DavidArmstrong/SAMDTelescopeController/TC4_0/tcheader.h

/* Telescope Controller 4.00.00 - Header file
// February 2026
// See MIT LICENSE.md file and ReadMe.md file for essential information
// Highly tailored to the AdaFruit M4 Metro
// DO NOT ATTEMPT TO LOAD THIS ONTO A STANDARD UNO */

#ifndef TC4_0_H
#define TC4_0_H
const char tcversion[] = "4.00.00";
/*=============================================================================
// Arduino SAMD Board Pin Definitions: digital from 0 to 13, Analog from 14 to 19
// D0 = Serial1 Rx - not needed, but can't be used elsewhere either
// D1 = Serial1 Tx - to 4x20 LCD
// D2 = Not Used
// D3 = Not Used
// D4 = Serial2 Rx - from XBee (Yellow wire on my cable) (SAMD51)
// Pins used for optional Reference sensors */

//const int HORIZONlim = 5; // D5 - Altitude axis Horizon reference point
//const int ZENITHlim = 6; // D6 - Altitude axis Zenith point
// D7 = Serial2 Tx - to XBee (Green wire on my cable) (SAMD51) */
const int AZREFsensor = 8; /* D8 - Azimuth axis reference point */

const int SPI_SS2 = 9; // D9 - telescope tube inclinometer sensor select
const int SPI_SS1 = 10; // D10 - Rocker Base inclinometer sensor select
// IR Detector Pin - Use TV/DVD IR Remote as a handbox control
const int IR_RECVpin = 11; /* D11 - IR Remote sensor */

// D12 = Not used
const int BLUE_LED = 13; // Blue "stat" LED on pin D13

/* D14 = A0 - Not Used
// Define Encoder Pins - Must have this if nothing else
const int RAAZ_pinA = 15; // A1 - Azimuth Encoder
const int RAAZ_pinB = 16; // A2
const int DECAL_pinA = 17; // A3 - Altitude Encoder
const int DECAL_pinB = 18; // A4 */
#define RAAZ_pinA   15
#define RAAZ_pinB   16
#define DECAL_pinA  17
#define DECAL_pinB  18

// Real Hardware button for forced re-init, position Lock, etc.
const int LOCKBTN = 19; /* A5 */
/*
// D22 = I2C SDA
// D23 = I2C SCL
// Use ICSP pins here for Murata SCA3300 inclinometer(s)
// D24 = MISO
// D26 = MOSI
// D25 = SCK */
//const int RX_LED = PIN_LED_RXL; // RX LED on pin 27, use the predefined PIN_LED_RXL to make sure
//const int TX_LED = PIN_LED_TXL; // TX LED on pin 28, use the predefined PIN_LED_TXL to make sure
/* D29-31 = USB
// D32-34 = Secondary SPI
// D35 - Secondary SPI cs

/*==========================================================================
  // I2C Addresses used
  // I2C HMC6343 Magnetic Compass (IIC address 0x19) (Not used nor referenced)
  // I2C MMC5983MA Magnetic Compass (IIC address 0x30)
  // I2C HMC6352 Magnetic Compass (IIC address 0x21, 0x41, 0x53, 0x57)
  // I2C HMC6343 Magnetic Compass (IIC address 0x32, 0x33)
  // I2C GPS receiver module (IIC address 0x42)
  // IIC address of EEPROM - 24LC256 or 24C512C-L */
//const int EEPROM_ADR = 0x55;
const int EEPROM_ADR = 0x50;
// Motor Driver config pattern "1000" on board for address 0x5D
const int MotorDriver_ADR = 0x5D; //Qwiic Motor Driver
const int LCDi2c_ADR = 0x72; //Default for Sparkfun OpenLCD
// BME280 Temperature, Barometric Pressure, Relative Humidity Sensoe I2C address
const int BME280_ADR = 0x77;

/*=======================================================================================
// Libraries!  This is why I use Arduino, seriously.

// Normally, Encoder uses attachInterrupt(), which allows dynamically attaching functions to each interrupt. The dynamic function call adds slight overhead. To eliminate this extra overhead, you can use this option. It must be defined before Encoder.h is included.
#define ENCODER_OPTIMIZE_INTERRUPTS
// This optional setting causes Encoder to use more optimized code
// The downside is a conflict if any other code in your sketch or any libraries you use require attachInterrupt(). */
#include <Encoder.h> //Optical Quadrature Encoders https://github.com/PaulStoffregen/Encoder

#include "wiring_private.h" // pinPeripheral() function for Serial2 UART
#include <Arduino.h>
#include "pins_arduino.h"
#include <Wire.h>  // Include Wire if you're using I2C
#include <stdint.h>
#include <string.h>

#include "RTC_SAMD51.h" // https://github.com/Seeed-Studio/Seeed_Arduino_RTC
#include "DateTime.h"

#include <math.h> //Oh yeah.....
#include "SiderealPlanets.h" //Astronomy routines https://github.com/DavidArmstrong/SiderealPlanets
#include "SiderealObjects.h" //Astronomy Tables https://github.com/DavidArmstrong/SiderealObjects
#include <curveFitting.h> // https://github.com/Rotario/arduinoCurveFitting

#include "extEEPROM.h" // I2C EEPROM https://github.com/PaoloP74/extEEPROM
#include <SerLCD.h> //Serial LCD library: https://github.com/sparkfun/SparkFun_SerLCD_Arduino_Library
#include "ansi.h" // VT100 support https://github.com/RobTillaart/ANSI
#include <SparkFun_u-blox_GNSS_Arduino_Library.h> //Click here to get the library: https://github.com/sparkfun/SparkFun_u-blox_GNSS_Arduino_Library
#include "SparkFunBME280.h" //Temperature, Pressure, Humidity sensor https://github.com/sparkfun/SparkFun_BME280_Arduino_Library

#include <IRLibDecodeBase.h> // First include the decode base https://github.com/cyborg5/IRLib2 
#include <IRLib_P01_NEC.h>   // Now include only the protocols you wish
#include <IRLib_P02_Sony.h>  // to actually use. The lowest numbered
#include <IRLib_P07_NECx.h>  // must be first but others can be any order.
//#include <IRLib_P09_GICable.h>
//#include <IRLib_P11_RCMM.h>
#include <IRLibCombo.h>     // After all protocols, include this
// All of the above automatically creates a universal decoder
// class called "IRdecode" containing only the protocols you want.
#include <IRLibRecv.h>

#include "SCMD.h" // Serial Controlled Motor Driver https://github.com/sparkfun/Serial_Controlled_Motor_Driver
#include "SCMD_config.h" //Contains #defines for common SCMD register names and values
#include "SAMD51_InterruptTimer.h"

// Magnetic Compass Libraries
#ifdef __HMC6352__
#include <HMC6352.h> // https://github.com/funflin/HMC6352-Arduino-Library
#endif
#ifdef __HMC6343__
#include "SFE_HMC6343.h" // https://github.com/sparkfun/SparkFun_HMC6343_Arduino_Library
#endif
#include <SparkFun_MMC5983MA_Arduino_Library.h> //Click here to get the library: http://librarymanager/All#SparkFun_MMC5983MA
// https://github.com/sparkfun/SparkFun_MMC5983MA_Magnetometer_Arduino_Library

#include "WMM_Tinier.h" // WMM Magnetic variation - https://github.com/DavidArmstrong/WMM_Tinier

#include <SPI.h> //Need for Murata inclinometer sensor
#include "SCL3300.h" // https://github.com/DavidArmstrong/Arduino-SCL3300

//=========================================
// EEPROM definitions
const int MAXUCOORD = 200; // maximum number of User Defined Coordinates
const int EEcheckByte = 0x54;
struct EEstruct {
  double dummy;
  double FtiltXrockeroff;
  double FtiltYrockeroff;
  double FtiltXtubeoff;
  double FtiltYtubeoff;
  double FLATITUDE;
  double FLONGITUDE;
  float DTEMPF; // default Farenheit temperature
  float DTZONE; // Default Time zone offset from GMT
  float azKp, azKi, azKd, alKp, alKi, alKd; // motor PID scaling values
  float azN, alN; // motor PID damping intervals
  // IR decode Table - 24 chars match one of 20 long numbers
  long IRinput[32]; // Raw IR remote button numbers
  char IRchar[32]; // Corresponding ASCII char for each number
  // User defined coordinates
  long UCOORD[MAXUCOORD * 2]; // save space for user defined objects
  long RRAAZ; //Default encoder range for RA/Azimuth
  long RDECAL; //Default encoder range for Declination/Altitude
  long AZOFFSET; //Encoder count Offset of Azimuth Reference Sensor from True North
  long ALOFFSET; //Encoder count Offset of Altitude Horizon Sensor from Level with horizon
  long AzTweakOffsetCounts, AlTweakOffsetCounts; // Count offsets based on last star sync
  int ELEVATION; // default elevation
  int EEchk;
  int LCDbrightness;
  int HbxSpeed;
  boolean DSTFLAG; // Set to true if Daylight Savings time is in effect
  boolean USELIMITS; //using Limits?
  boolean ERRFLAG; // error variable flag
  boolean PFLAG;  // Precession flag
  boolean RFLAG;  // True if Refraction calculations enabled
  boolean MotorDriverflag;
  boolean LCDserialflag; // PIC-based LCD display used?
  boolean LCDavrflag; // OpenLCD I2C display used?
  //Note: if both LCDserialflag and LCDavrflag are true, then an OpenLCD device is on TC_LCD
  boolean IRSETUPflag; // Set if IR remote has been set up
  boolean TCIFLAG; // Set if Telescope Control interface is configured
  boolean INA219flag; // INA219 I2C voltage monior used?
  char SiteID[40];
  boolean SerialTermflag; // Serial Terminal output Updated regularly?
  boolean AzRangeMeasured;
  boolean enableRealHwInit;
};

union EEarray {
  EEstruct strunion;
  byte ebuf[sizeof(EEstruct)];
} eecharbuf;

// 256 kbits = 32K bytes for EEPROM
//extEEPROM tcEEPROM(kbits_256, 1, 64, EEPROM_ADR);
// 512 kbits = 64K bytes for EEPROM
extEEPROM tcEEPROM(kbits_512, 1, 64, EEPROM_ADR);

//=======================================================
// Structure to hold data
// We need to populate this when we calculate data
struct DobsonianControlData {
  public:
    long int azimuthEncoder;
    long int altitudeEncoder;
    long int maxAzimuthCount;
    long int maxAltitudeCount;
    long int azimuthOffset;
    long int altitudeOffset;
    float declination; // magnetic variation from True North
};

DobsonianControlData spData;

/*=======================================================
  // Define stuff for compatibility with translated
  // Telescope Controller code (Originally in Forth)
  // Commands available in the system */
#define SETIMECMD 0x1c
#define FNDOBJECT 0x1d
#define INITCMD 0x1e
#define FNDARB 0x1f
// Stay at current telescope position
#define STAYFUNC 0x22

// Motor Defines to make it more readable
#define ALTITUDE_MOTOR 0
#define AZIMUTH_MOTOR 1
#define CW_DIRECTION 0
#define CCW_DIRECTION 1
#define STOP_SPEED 0
#define SLOW_SPEED 5
#define FAST_SPEED 255

// User variables
long IRkey; // Record latest raw IR key code, if seen
boolean lockbtninitflag;
byte COMMAND; //What the User tells us to do
byte screenCOMMAND;
boolean screenDecRefresh;
byte LCDscreenNum;
boolean TCIFLAG; // Set to true if Telescope Control interface has been set up
boolean displayFLAG; // Set to true if display option has been selected
boolean AUTOSTARFLAG;  // Set to true if system can offer to select alignment star
boolean INITFLAG;  // Telescope mount initialized flag
boolean TIMEFLAG;  // Time initialized flag
boolean DSTFLAG;  // Set to true if Daylight Savings time is in effect
boolean DSTAUTOFLAG; // Set to true if we automatically compute if DST is in effect - US Only

byte inputstrlen;

long RAAZ;  // Current encoder counts in RA/Azimuth
long DECAL;  // Current encoder counts in Declination/Altitude
long TcRAAZ;  // Target encoder counts in RA/Azimuth
long TcDECAL;  // Target encoder counts in Declination/Altitude
long RRAAZ;  // Known rangle of encoder counts in RA/Azimuth
long RDECAL;  // Known rangle of encoder counts in Declination/Altitude
double previousTRA, previousTDEC;
double TAZIMUTH; // Target Azimuth in degrees from North - used in Displays
double TALTITUDE; // Target Altitude in degrees

long LATEMP;
double FALTEMP;  // store floating # altitude
int GRYEAR;
byte GRMONTH, GRDAY;
long TIMER; //Double seconds time count
int rtcseconds, rtcmin, rtchours;
int hmsseconds, hmsmin, hmshours;
char siteid[70];

double FLONGITUDE, FLATITUDE;  // degrees
double FAZIMUTH, FALTITUDE; // degrees
double FRA, FDEC; // Current RA in hours, Declination in degrees
double TRA;  // Target RA in hours
double TDEC;  // Target Declination in degrees

boolean ERRFLAG;  // error variable flag
double FHEIGHT;  // FP elevation in feet
double FTEMPF;  // Temperature in Farenheit for refraction
double FHUMID; // Percent relative humidity
double FPINHG;  // Barometric Pressure in Inches of Mercury
double FELAT;  // Equatorial Mount Latitude
double FMAGHDG; // Magnetic Compass heading
float magVariation; // Magnetic Declination or Variation
long magVariationInAzimuthCounts;
long AzimuthMagneticEncoderOffset;
boolean magOffsetComputed;
long AzTweakOffsetCounts, AlTweakOffsetCounts;
int LCDbrightness;

// need to make auto star select table
const int ISTARS[] = {
  98  , /* Aldebaran */         492 , /* Vega */
  113 , /* Rigel */             529 , /* Altair */
  114 , /* Capella */           547 , /* Deneb */
  140 , /* Betelgeuse */        595 , /* Markab */
  162 , /* Sirius */            43  , /* Hamal */
  190 , /* Procyon */           30  , /* Achernar */
  196 , /* Pollux */            47  , /* Mira */
  188 , /* Castor */            62  , /* Algol */
  254 , /* Regulus */           155 , /* Canopus */
  350 , /* Arcturus */          330 , /* Mizar */
  422 , /* Antares */           592   /* Fomalhaut */
};
const byte NISTARS = 22; // number of stars in table

const char hitkey[] = "Hit Key to continue";

// define IR receive pin - for IR Remote Library routines
int RECV_PIN = IR_RECVpin;
//decode_results results;
boolean irsetup, IRFLAG;
char irkeytab[20];

/*======================================================================
// Library specific variable defines
// For second UART port - SAMD51 can only have TX on PAD 0 */
#define PIN_SERIAL2_RX 4    /* PB13 */
#define PAD_SERIAL2_RX (SERCOM_RX_PAD_1)
#define PIN_SERIAL2_TX 7    /* PB12 */
#define PAD_SERIAL2_TX (UART_TX_PAD_0)
Uart Serial2( &sercom4, PIN_SERIAL2_RX, PIN_SERIAL2_TX, PAD_SERIAL2_RX, PAD_SERIAL2_TX );
Stream *SERIALOUT = &Serial2;
/* RX: SERCOM4/PAD[1] = D4 = PB13
// TX: SERCOM4/PAD[0] = D7 = PB12 */

#ifndef SWAP_AZIMUTH_ENCODER_AB
Encoder RAAZenc( RAAZ_pinA , RAAZ_pinB ); //Incremental Quadrature Encoder for RA/Aximuth
#else
Encoder RAAZenc( RAAZ_pinB , RAAZ_pinA ); //Incremental Quadrature Encoder for RA/Aximuth
#endif

// Now declare an instance of that decoder.
IRdecode irdecoder;
IRrecv irrecv(RECV_PIN);  //pin number for the receiver
RTC_SAMD51 rtczero;

BME280 bme280; //Temperature, Barometric Pressure, Humidity Sensor
SFE_UBLOX_GNSS ubloxGPS;
boolean I2CEEPROMpresent, GPSpresent, BMEpresent;
SiderealPlanets myAstro;
SiderealObjects myObjects;
boolean MotorDriverflag;
SCMD i2cMotorDriver; //Serial Controlled Motor Driver

boolean MagCompasspresent;
boolean HMC6343MagCompasspresent;
boolean MMC5983MAMagCompasspresent;
#ifdef __HMC6343__
SFE_HMC6343 dobHMC6343; // Declare the compass object
#endif
SFE_MMC5983MA MMC5983MAmag;
WMM_Tinier myDeclination;
SCL3300 rockerTilt, tubeTilt; // inclinometers
boolean rockerTiltPresent, tubeTiltPresent;
ANSI ansi(&TCterminal); // VT100 support
boolean AzimuthEncoderInitialized;
int currentAzMtrSpeed, currentAlMtrSpeed;
int currentAzMtrDir, currentAlMtrDir;
unsigned long AzPreviousMillis, AlPreviousMillis;
float azKp, azKi, azKd, alKp, alKi, alKd; // motor PID scaling values
float azN, alN; // motor PID damping intervals
float azTau, alTau;
float azError[3] = { 0., 0., 0. };
float alError[3] = { 0., 0., 0. };
float azD0, azD1, azFd0, azFd1;
float alD0, alD1, alFd0, alFd1;
boolean PIDFLAG;

#ifndef __FUNCTIONDECLARATIONS__
//===============================================
// need to declare all functions - whatever
// TCVCIOFP
char KEY();
void EMIT(char n);
long GETnum(char* buf);
void LCDline1();
void LCDline2();
void LCDline3();
void LCDline4();
void LCDclear();
void LCDbrighter();
void LCDdimmer();
void LCDprint(int tmp);
void LCDprint(long tmp);
void LCDprint(double tmp, int frac);
void LCDprint(char tmp);
void LCDprint(char* tmp);
void LCDprint(const char* tmp);
void SETINITFLAG();
void RESETINITFLAG();
boolean NOTINITquestion();
void SETIMEFLAG();
void RESETIMEFLAG();
boolean NOTIMESETquestion();
boolean INITCOMMANDquestion();
boolean TIMECOMMANDquestion();
void SETIRFLAG();
void RESETIRFLAG();
boolean IRquestion();
void SETTCIFLAG();
void RESETTCIFLAG();
boolean TCIquestion();
void SETdisplayFLAG();
void RESETdisplayFLAG();
boolean Displayquestion();
void SETPIDFLAG();
void RESETPIDFLAG();
boolean PIDquestion();
void SETERRFLAG();
void RESETERRFLAG();
int ACCEPT(char *buf, int limit);
boolean RDLBTN();
void TERMclear();
void TERMlineup();
void TERMcursor();
void TERMxy(int x, int y);
void TERMtextcolor( char buf );
void WAITASEC(int n);
void newdelay( long interval );
boolean CHKNUM();
#ifdef __HMC6352__
boolean getMagCompassPresent(void);
#endif
#ifdef __HMC6343__
boolean get6343MagCompassPresent(void);
#endif
float magneticDeclination(float Latitude, float Longitude, uint8_t year, uint8_t month, uint8_t day);
float getMagCompassHeading(void);
double getMMC5983MagCompassHeading(void);
boolean getRockerTiltPresent(void);
boolean getTubeTiltPresent(void);
double getAltitude(void);
double getAzimuth(void);
boolean getAzRefSensor();
boolean startMotorToTarget(int motor, int direction, unsigned long currentPosition, unsigned long targetPosition);
boolean driveMotor(int motor, int direction, int speed);
boolean driveMotorStop(int motor);

// TCDERVIO
void printDegMinSecs(double n);
void printDegMinSecsLCD(double n);
void printTime(double n);
void printTimeLCD(double n);
void print2digits(int number);
void print2digitsUSB(int number);
void print2digitsLCD(int number);
boolean TRPLCMP( int n1, int n2, int n3, int n4 );
boolean GETYORN();
long GETDDECNUM();
int GETINUM();
int GETINUM(int n);
long CONVHMS(char *buf);
long INPUTHMS();
double GETFDECNUM();
double GETFDECNUM(float n);

// TCUSERIO
void printstatusscreen();
void showDate();
void showDateLCD();
void printObject();
void printObjectLCD();
void updatestatusscreen();
void updatestatusLCD();
void TERMALLOPTIONS();
void PRPLANET( int n );
void PRPLANETlcd( int n );

// TCINIT
void SERCOM4_0_Handler();
void SERCOM4_1_Handler();
void SERCOM4_2_Handler();
void SERCOM4_3_Handler();
void eepromDefaults();
void rockertiltlevelcheck();
void gotoAzRef();
void measureAZrange();
void getMagneticNorth();
double getTubeTiltX();
void inithardware();
void STRTturboCLK();
void INITZONE();
void RESETIME();
void INIT();
long initIRkey(long previous);
void RESETIR();
void OptionStateMsg(boolean flag);
void LCDOptionStateMsg(boolean flag);
void RESETTCI();
void RESETdisplay();
void topEEPROMwrite();
void gotoTarget();
void doCommand();
void tcintro();
void TC_main();
#endif
#endif
