DavidArmstrong/SAMDTelescopeController/TC4_0/tcinit.ino

/* Telescope Controller 4.00.00 - Initialization and High level functionality
// February 2026
// See MIT LICENSE.md file and ReadMe.md file for essential information
// Highly tailored to the AdaFruit M4 Metro
// DO NOT ATTEMPT TO LOAD THIS ONTO A STANDARD UNO */

#include "tcheader.h"

/* We have to define this function to use the SAMD51 alternate Serial2 pins
// And for SAMD51 on the Metro M4 - can't use sercom5, 3, or 2
// sercom3 - Serial1 on D0/D1
// sercom5 - I2C pins for SCL/SDA
// sercom2 - SPI */
#ifdef _VARIANT_SAMD51_MICROMOD_
#else
void SERCOM4_0_Handler() { Serial2.IrqHandler(); }
void SERCOM4_1_Handler() { Serial2.IrqHandler(); }
void SERCOM4_2_Handler() { Serial2.IrqHandler(); }
void SERCOM4_3_Handler() { Serial2.IrqHandler(); }
#endif

void eepromDefaults() {
  // Default values that we start with on a new EEPROM
  IRkey = 0L;
  // Brute force default initialization of EEPROM variables
  // We will replace the defaults if valid data is in an EEPROM
  eecharbuf.strunion.EEchk = 0; // Check for existence of EEPROM
  //eecharbuf.strunion.DSTFLAG = false; // Daylight Savings used
  eecharbuf.strunion.USELIMITS = false; // Using Limit/reference sensors?
  eecharbuf.strunion.ERRFLAG = false; // Errors flag
  eecharbuf.strunion.PFLAG = false; // Precession flag
  eecharbuf.strunion.RFLAG = false; // Refraction flag
  eecharbuf.strunion.MotorDriverflag = false; // Motor driver flag
  eecharbuf.strunion.SerialTermflag = true; // Serial port Terminal display
  eecharbuf.strunion.LCDserialflag = false; // PIC-based or AVR-based LCD on Serial used?
  eecharbuf.strunion.LCDavrflag = false; // AVR LCD on IIC?
  eecharbuf.strunion.LCDbrightness = 255; // Full brightness for LCD backlight
  eecharbuf.strunion.IRSETUPflag = irsetup = false; // IR remote in use
  eecharbuf.strunion.TCIFLAG = TCIFLAG = false; // Telescope Control Interface set up
  eecharbuf.strunion.ELEVATION = 5500; // Elevation in feet
  eecharbuf.strunion.RRAAZ = 10000L; // Azimuth encoder range
  eecharbuf.strunion.RDECAL = pow(2, 14); // Altitude encoder range
  eecharbuf.strunion.AZOFFSET = 0L; // Encoder count Offset of Azimuth Reference from True North
  eecharbuf.strunion.ALOFFSET = 0L; // Encoder count Offset of Altitude Horizon Reference from level
  eecharbuf.strunion.AzTweakOffsetCounts = 0L; // Count offsets based on last star sync
  eecharbuf.strunion.AlTweakOffsetCounts = 0L;
  AzTweakOffsetCounts = AlTweakOffsetCounts = 0L;
  eecharbuf.strunion.DTEMPF = 68.0; // Default temp in Farenheit
  //eecharbuf.strunion.DTZONE = -8.0; // Default Time Zone (PST)
  eecharbuf.strunion.FLATITUDE = 1.; // Latitude in radians
  eecharbuf.strunion.FLONGITUDE = -1.; // Longitude in radians, West is negative
  strncpy ( eecharbuf.strunion.SiteID, "Demo mode", sizeof("Demo mode") );
  eecharbuf.strunion.AzRangeMeasured = false;
  eecharbuf.strunion.FtiltXrockeroff = 0.; // Offset of X Tilt on Rocker from level
  eecharbuf.strunion.FtiltYrockeroff = 0.; // Offset of Y Tilt on Rocker from level
  eecharbuf.strunion.FtiltXtubeoff = 0.; // Offset of X Tilt on Telescope Tube from level
  eecharbuf.strunion.FtiltYtubeoff = 0.; // Offset of Y Tilt on Telescope Tube from level
  // Set up default values for Demo mode
  //DSTFLAG = eecharbuf.strunion.DSTFLAG;
  // Assume Demo mode on initial boot
  eecharbuf.strunion.enableRealHwInit = false;
  MotorDriverflag = eecharbuf.strunion.MotorDriverflag;
  // PID scaling values - We guess at these, or determine them empirically
  eecharbuf.strunion.azKp = 1.0; // Azimuth motor Proportional gain
  eecharbuf.strunion.azKi = 1.0; // Azimuth motor Integral gain
  eecharbuf.strunion.azKd = 1.0; // Azimuth motor Derivative gain
  eecharbuf.strunion.azN  = 5; // Azimuth derivative low pass filter time constant, 3 <= N <= 10
  eecharbuf.strunion.alKp = 1.0; // Altitude motor Proportional gain
  eecharbuf.strunion.alKi = 1.0; // Altitude motor Integral gain
  eecharbuf.strunion.alKd = 1.0; // Altitude motor Derivative gain
  eecharbuf.strunion.alN  = 5; // Altitude derivative low pass filter time constant, 3 <= N <= 10
  // Offset of Azimuth Encoder Range from measured Magnetic North
  AzimuthMagneticEncoderOffset = 0.;
  magOffsetComputed = false;
  LCDbrightness = 0x9D; // Default LCD backlight brightness is MAX
  RAAZenc.write(0L);
  FAZIMUTH = 0.;
  //DECALenc.write(0L);
  FALTITUDE = 0.;
}

void rockertiltlevelcheck() {
  // Telescope should already be parked on boot so leveling access holes are reachable
  int i = 0;

  TCterminal.println("");
  TCterminal.println("Check Rocker Level:");
  TCterminal.println(hitkey);

  LCDline2();
  LCDprint("Check Level:");
  LCDline4();
  LCDprint(hitkey);

  while (!CHKNUM()) {
    if (rockerTilt.isConnected()) {
      //Get next block of data from sensor
      if (rockerTilt.available()) {
        if (eecharbuf.strunion.SerialTermflag) {
          // print Base tilt
          TCterminal.println("");
          TCterminal.print(rockerTilt.getTiltLevelOffsetAngleX() - eecharbuf.strunion.FtiltXrockeroff);
          TCterminal.print("  ");
          TCterminal.print(rockerTilt.getTiltLevelOffsetAngleY() - eecharbuf.strunion.FtiltYrockeroff);
          TCterminal.print("  ");
          TERMlineup();
          LCDline3();
          LCDprint(rockerTilt.getTiltLevelOffsetAngleX() - eecharbuf.strunion.FtiltXrockeroff, 2);
          LCDprint("  ");
          LCDprint(rockerTilt.getTiltLevelOffsetAngleY() - eecharbuf.strunion.FtiltYrockeroff, 2);
          LCDprint("  ");
          newdelay(500);
        }
        } else rockerTilt.reset();
      } else rockerTilt.reset();
    }
    KEY();
  TCterminal.println("");
  LCDclear();
}

void gotoAzRef() {
  //If Azimuth Reference Sensor, use that
  if (eecharbuf.strunion.USELIMITS) {
    // Start by finding the Azimuth Reference Sensor.
    if (getAzRefSensor()) {
      // We're on the sensor, so get off it.
      if (MotorDriverflag) {
        //Run the motor CCW to get off of it
        driveMotor(AZIMUTH_MOTOR, CCW_DIRECTION, FAST_SPEED);
      } else {
        TCterminal.println("Move telescope in Azimuth CCW to get off of AZ Reference Sensor.");
        TCterminal.println(hitkey);
        LCDclear();
        LCDline2();
        LCDprint("Move Azimuth CCW");
        LCDline4();
        LCDprint(hitkey);
        KEY();
      }
      // And wait....
      while (getAzRefSensor()) ;
      driveMotorStop(AZIMUTH_MOTOR); // Turn motor off
    }
    if (MotorDriverflag) {
      newdelay(500);
      // Start motor in CW direction to find Azimuth Reference Sensor
      driveMotor(AZIMUTH_MOTOR, CW_DIRECTION, FAST_SPEED);
    } else {
      TCterminal.println("Move telescope in Azimuth CW to find AZ Reference Sensor.");
      LCDclear();
      LCDline2();
      LCDprint("Move Azimuth CCW");
    }
    // Continue  until we find the AZ ref sensor
    while (!getAzRefSensor()) ;
    // We hit it, so zero the Encoder counts
  } else {
    TCterminal.println("Move telescope in Azimuth to select an AZ Reference position. (i.e. North)");
    TCterminal.println(hitkey);
    LCDclear();
    LCDline1();
    LCDprint("Move Azimuth");
    LCDline2();
    LCDprint("to Reference Pt");
    LCDline3();
    LCDprint("(i.e. North)");
    LCDline4();
    LCDprint(hitkey);
    KEY();
  }
  RAAZenc.write(0L);
  RAAZ = 0L;
}

void measureAZrange() {
  // Need to play the game to measure how many encoder counts make one revolution in Azimuth
  gotoAzRef();
  // And keep going to get off the sensor
  if (!MotorDriverflag) {
    TCterminal.println("Keep moving telescope in Azimuth CW to find AZ Reference ");
    LCDclear();
    LCDline1();
    LCDprint("Move Azimuth CW");
    LCDline2();
    
    if (eecharbuf.strunion.USELIMITS) {
      TCterminal.println("Sensor again.");
      LCDprint("to Reference Pt");
    } else {
      TCterminal.println("position again. (i.e. North)");
      LCDprint("to North");
    }
    LCDline3();
    LCDprint("again");
  }
  
  if (eecharbuf.strunion.USELIMITS) {
    while (getAzRefSensor()) ;
    // And keep running until we hit the AZ ref sensor again
    newdelay(100);
    while (!getAzRefSensor()) ;
  } else {
    TCterminal.println(hitkey);
    LCDline4();
    LCDprint(hitkey);
    KEY();
  }
  RAAZ = RRAAZ = eecharbuf.strunion.RRAAZ = RAAZenc.read();
  eecharbuf.strunion.AzRangeMeasured = true;
  AzimuthEncoderInitialized = true;
  if (!MotorDriverflag) {
    if (eecharbuf.strunion.USELIMITS) TCterminal.print("Hit AZ Reference Sensor again. ");
    TCterminal.print("AZ Range is: ");
    TCterminal.print(eecharbuf.strunion.RRAAZ);
    LCDclear();
    LCDline1();
    LCDprint("AZ Range is:");
    LCDline2();
    LCDprint(RRAAZ);
  } else {
    driveMotorStop(AZIMUTH_MOTOR); // Stop motor and From now on, ignore the Azimuth Reference Sensor
  }
  newdelay(500);
  // Next, we need the offsets for the Rocker inclinometer in X and Y from true level
  if (getRockerTiltPresent()) {
    double FtiltXrockerHi = 0.;
    double FtiltYrockerHi = 0.;
    double FtiltXrockerLo = 0.;
    double FtiltYrockerLo = 0.;
    double Xtilt, Ytilt;
    rockerTilt.setFastReadMode();
    if (!MotorDriverflag) {
      TCterminal.println("Move telescope in Azimuth back around CCW to find AZ Inclinometer Offsets.");
      LCDclear();
      LCDline1();
      LCDprint("Move Azimuth CCW");
      LCDline2();
      LCDprint("to find");
      LCDline3();
      LCDprint("SCL3300 offsets");
    } else {
      // Turn Azimuth motor on CCW towards zero
      driveMotor(AZIMUTH_MOTOR, CCW_DIRECTION, SLOW_SPEED);
    }
    while ( RAAZenc.read() > 0 ) {
      //Get next block of data from sensor
      if (rockerTilt.available()) {
        // print Base tilt
        Xtilt = rockerTilt.getTiltLevelOffsetAngleX();
        Ytilt = rockerTilt.getTiltLevelOffsetAngleY();
        if (Xtilt > FtiltXrockerHi) FtiltXrockerHi = Xtilt;
        if (Xtilt < FtiltXrockerLo) FtiltXrockerLo = Xtilt;
        if (Ytilt > FtiltYrockerHi) FtiltYrockerHi = Ytilt;
        if (Ytilt < FtiltYrockerLo) FtiltYrockerLo = Ytilt;
      } else rockerTilt.reset();
    }
    rockerTilt.stopFastReadMode();
    eecharbuf.strunion.FtiltXrockeroff = (FtiltXrockerHi + FtiltXrockerLo) / 2.;
    eecharbuf.strunion.FtiltYrockeroff = (FtiltYrockerHi + FtiltYrockerLo) / 2.;
    if (!MotorDriverflag) {
      TCterminal.println("AZ Inclinometer Offsets computed.");
    } else {
      // And turn motor Off
      driveMotorStop(AZIMUTH_MOTOR);
    }
    //`Allow User to Level the Bottom Board now....
    rockertiltlevelcheck();
  }
}

void getMagneticNorth() {
  // Use a magnetic compass to figure out the offset between the current
  // Azimuth zero reference point, and Magnetic North
  int order = 1;
  double x[3600], y[3600], n;
  double x0[3600], y0[3600], n0;
  double coeffs[order+1];
  char buf[100];
  int i, j, max, min, guessNorth;
  
  // We only do this if we are using Motors so as to avoid magnetic noise
  if (MotorDriverflag && (
#ifdef __HMC6352__
  getMagCompassPresent() ||
#endif
#ifdef __HMC6343__
  HMC6343MagCompasspresent ||
#endif
  MMC5983MAMagCompasspresent)) {
    // Prompt User to prep for Magnetic Compass
	TCterminal.println("");
    TCterminal.println("Check Magnetic Compass position:");
    TCterminal.println(hitkey);
    LCDclear();
    LCDline1();
    LCDprint("Check Mag Compass");
    LCDline4();
    LCDprint(hitkey);
	KEY();
#ifdef __HMC6352__
	if (getMagCompassPresent()) {
	  HMC6352.Wake();
      newdelay(10);
	}
#endif
	// We start with a game to get a 'full' circle in Azimuth
	driveMotor(AZIMUTH_MOTOR, CCW_DIRECTION, FAST_SPEED); // Go backwards past zero point
	while (RAAZenc.read() > 0L) ; // wait until past it
	driveMotorStop(AZIMUTH_MOTOR); // Stop the motor
	// Turn Azimuth motor on going CW around
	driveMotor(AZIMUTH_MOTOR, CW_DIRECTION, FAST_SPEED);
	while (RAAZenc.read() < 0L) ; // wait until we reach zero
    // GO! - Get data points - Assume we are starting at Azimuth = 0
	y[3599] = 0.;
    for (i = 0; i < 3600; i++) {
	  // wait until we get to the next point
	  while ((RAAZenc.read() * 3600L / RRAAZ) % 3600L != 0L) ;
	  x[1] = (double) RAAZenc.read();
#ifdef __HMC6352__
	  if (getMagCompassPresent()) y[i] = (double) HMC6352.GetHeading();
#endif
	  if (MMC5983MAMagCompasspresent) y[i] = getMMC5983MagCompassHeading();
	  while ((RAAZenc.read() * 3600L / RRAAZ) % 3600L == 0L) ; // wait until off this point
	}
	driveMotorStop(AZIMUTH_MOTOR); // Stop the motor
	// Now we most likely have a sawtooth pattern of magnetic readings
	// Need to move the data points around so it's more-or-less a line
	// Start by finding the max and min magnetic compass points in the array
	max = 0;
	min = 3600;
	for (i = 0; i < 3600; i++) {
      if (y[i] > y[max]) max = i;
	  if (y[i] < y[min]) min = i;
	}
	// We guess that average between min and max is where magnetic North is
	guessNorth = (max + min) / 2;
	// And shift the data arrays accordingly so we can do a reasonable curve fit
    for (i = 0; i < 3599; i++) {
      j = i + guessNorth;
	  if (j > 3599) {
        j -= 3600;
	  }
	  y0[i] = y[j]; // Magnetic Compass reading
	  x0[i] = x[j]; // Encoder position
	}
	TCterminal.print("Needed to shift array by about ");
	TCterminal.print(guessNorth * (RRAAZ / 3600L));
	TCterminal.println(" encoder counts");
	// And now we do the curve fit
    int ret = fitCurve(order, sizeof(y0)/sizeof(double), x0, y0, sizeof(coeffs)/sizeof(double), coeffs);
  
    if (ret == 0) { //Returned value is 0 if no error
      uint8_t c = 'a';
      TCterminal.println("Coefficients are");
      for (int i = 0; i < sizeof(coeffs)/sizeof(double); i++) {
        snprintf(buf, 100, "%c=",c++);
        TCterminal.print(buf);
        TCterminal.print(coeffs[i]);
        TCterminal.print('\t');
      }
	  // Save Magnetic offset
      // Later, it will be used with Magnetic Variation, and current Azimuth range
	  // So that location '0' is True North
	  AzimuthMagneticEncoderOffset = ((float)guessNorth * ((float)RRAAZ / 3600.)) + (-coeffs[1] / coeffs[0]);
    } else {
	  TCterminal.println("Error in computing Curve fit of data");
	  TCterminal.println("Making a guess of where Magnetic North is in Encoder counts.");
	  AzimuthMagneticEncoderOffset = (float)guessNorth * ((float)RRAAZ / 3600.);
    }
	magOffsetComputed = true;
	TCterminal.println("");
    TCterminal.println("Retract Magnetic Compass position:");
    TCterminal.println(hitkey);
    LCDclear();
    LCDline1();
    LCDprint("Retract Mag Compass");
    LCDline4();
    LCDprint(hitkey);
	KEY();
  }
}


double getTubeTiltX() {
  // Return only the Telescope Optical tube tilt in the X direction on the sensor
  // We will do this by cheating horribly and accept a value even if there is an error
  tubeTilt.available();
  return tubeTilt.getTiltLevelOffsetAngleX();
}

void inithardware() { //Set up all the hardware interfaces
  // Read Hardware button for forced re-init, position Lock, etc.
  pinMode(LOCKBTN, INPUT_PULLUP);
  lockbtninitflag = RDLBTN(); //Get button state, first thing
  // initialize digital pin LED_BUILTIN as an output.
  pinMode(LED_BUILTIN, OUTPUT);
  pinMode(AZREFsensor, INPUT_PULLUP);
  
  eepromDefaults();
  AzimuthEncoderInitialized = false;

  // verify presence of I2C EEPROM
  byte EEPROMstatus = tcEEPROM.begin(extEEPROM::twiClock100kHz);
  I2CEEPROMpresent = true;
  if ( EEPROMstatus != 0 ) {
    I2CEEPROMpresent = false;
    //lockbtninitflag = true; //Force demo mode
  } else { // /*
    // Read in EEPROM values
    int testbyte = tcEEPROM.read(0L + EEOFFSET); // read first byte in EEPROM
    if (testbyte == EEcheckByte) {
      // Good data there, so read in the rest of the array
      int eestat = tcEEPROM.read(2L + EEOFFSET, eecharbuf.ebuf, sizeof(EEstruct));
      if (eestat == 0) {
        DSTFLAG = eecharbuf.strunion.DSTFLAG;
        irsetup = eecharbuf.strunion.IRSETUPflag;
        TCIFLAG = eecharbuf.strunion.TCIFLAG;
		// PID scaling values
        azKp = eecharbuf.strunion.azKp; // Azimuth motor Proportional gain
        azKi = eecharbuf.strunion.azKi; // Azimuth motor Integral gain
        azKd = eecharbuf.strunion.azKd; // Azimuth motor Derivative gain
        azN  = eecharbuf.strunion.azN;  // Azimuth derivative low pass filter time constant
        alKp = eecharbuf.strunion.alKp; // Altitude motor Proportional gain
        alKi = eecharbuf.strunion.alKi; // Altitude motor Integral gain
        alKd = eecharbuf.strunion.alKd; // Altitude motor Derivative gain
        alN  = eecharbuf.strunion.alN;  // Altitude derivative low pass filter time constant
      } else {
		LCDline4(); LCDprint("EEPROM read error ");
	  }
    }
    eecharbuf.strunion.EEchk = EEcheckByte; // */
  }
  
  if (RRAAZ != 0L) {
    // zero the Encoder counts
    RAAZenc.write(0L);
    RAAZ = 0L;
    eecharbuf.strunion.AzRangeMeasured = true;
    eecharbuf.strunion.RRAAZ = RRAAZ;
  }
  if (RDECAL != 0L) {
    // We know the range
    // So just set the range count accordingly
    eecharbuf.strunion.RDECAL = RDECAL;
  }

  if (eecharbuf.strunion.LCDavrflag || eecharbuf.strunion.LCDserialflag) {
    LCDclear(); // Only clear if we are using LCD display
    newdelay(500);
    LCDline1();
    LCDprint("TC ");
    LCDprint(tcversion);
    LCDprint("    ");
  }
  if (I2CEEPROMpresent) {
    TCterminal.println("I2C EEPROM detected.");
  } else {
    TCterminal.println("I2C EEPROM *NOT* detected.");
  }

  rockerTiltPresent = false;
  tubeTiltPresent = false;
  if (rockerTilt.begin(SPI_SS1)) {
    rockerTiltPresent = true;
    TCterminal.println("Rocker Murata SCL3300 inclinometer detected.");
  }
  if (tubeTilt.begin(SPI_SS2)) {
    tubeTiltPresent = true;
    TCterminal.println("Tube/Altitude Murata SCL3300 inclinometer detected.");
    // Put this inclinometer into Mode 1, since we are using it to measure 0-90 Degree angles
    tubeTilt.setMode(1);
    if (tubeTilt.begin(SPI_SS2)) {
      TCterminal.println("Tube/Altitude Murata SCL3300 inclinometer now in Mode 1.");
	} else {
      tubeTiltPresent = false;
      TCterminal.println("Tube/Altitude Murata SCL3300 inclinometer failed to transition to Mode 1.");
	}
  }

  if (getRockerTiltPresent() && eecharbuf.strunion.enableRealHwInit) {
    // If we don't know the Azimuth encoder range, We'll get that first, 
    // with the Rocker tilt offsets, before doing the Level check later on
    if (eecharbuf.strunion.AzRangeMeasured) {
      TERMtextcolor('g');
      rockertiltlevelcheck();
      TERMtextcolor('c');
    }
  }
  
  myDeclination.begin(); // Initialize magnetic variation calculations
  // Check for various magnetic compass hardware
#ifdef __HMC6352__
  HMC6352.Wake();  // This is the really old EOL compass
  newdelay(20);
  FMAGHDG = HMC6352.GetHeading();
  HMC6352.Sleep();
#endif

  MMC5983MAMagCompasspresent = false; // This is the latest hardware available
  HMC6343MagCompasspresent = false;  // This is the more accurate hardware
#ifdef __HMC6352__
  if (FMAGHDG > 360.1) { //Old Magnetic Compass not detected at default I2C address
    MagCompasspresent = false;
#endif

#ifdef __HMC6343__
    // Initialize the HMC6343 and verify its physical presence
    if (dobHMC6343.init()) {
      TCterminal.println("HMC6343 Magnetic Compass detected.");
      HMC6343MagCompasspresent = true;
    }
#endif
    if (MMC5983MAmag.begin()) {
      TCterminal.println("MMC5983MA Magnetic Compass detected.");
      MMC5983MAMagCompasspresent = true;
      MMC5983MAmag.softReset();
    }
#ifdef __HMC6352__
  } else { // Old Magnetic Compass online
    MagCompasspresent = true;
    TCterminal.println("HMC6352 Magnetic Compass detected.");
  }
#endif

  byte bme280_id = bme280.begin(); //Returns ID of 0x60 if successful
  if (bme280_id != 0x60) { // Problem with BME280
    BMEpresent = false;
  } else { // BME280 online
    BMEpresent = true;
    TCterminal.println("BME280 Humidity, Barometric Pressure and Temperature sensor detected.");
    bme280.settings.commInterface = I2C_MODE;
    bme280.settings.I2CAddress = BME280_ADR;
    bme280.settings.runMode = 3; //Forced mode
    bme280.settings.tStandby = 0;
    bme280.settings.filter = 4;
    bme280.settings.tempOverSample = 5;
    bme280.settings.pressOverSample = 5;
    bme280.settings.humidOverSample = 5;
  }
  newdelay(100);
  
  // Have to have motor driver set up before we can start initializing the mount
  MotorDriverflag = eecharbuf.strunion.MotorDriverflag;
  currentAzMtrSpeed = currentAlMtrSpeed = 0;
  currentAzMtrDir = currentAlMtrDir = CW_DIRECTION;
  AzPreviousMillis = AlPreviousMillis = millis();
  azD0 = azD1 = azFd0 = azFd1 = 0.0;
  alD0 = alD1 = alFd0 = alFd1 = 0.0;
  azTau = azKd / (azKp*azN); // Azimuth IIR filter time constant
  alTau = alKd / (alKp*alN); // Altitude IIR filter time constant
  if (MotorDriverflag && eecharbuf.strunion.enableRealHwInit) {
    TCterminal.println("Motor driver setup.");
    i2cMotorDriver.settings.commInterface = I2C_MODE;
    i2cMotorDriver.settings.I2CAddress = MotorDriver_ADR;
    while ( i2cMotorDriver.begin() != 0xA9 ) //Wait until a valid ID word is returned
    {
      TCterminal.println( "ID mismatch, trying again" );
      newdelay(500);
    }
    TCterminal.println( "ID matches 0xA9" );
    //  Check to make sure the driver is done looking for peripherals before beginning
    TCterminal.print("Waiting for enumeration...");
    while ( i2cMotorDriver.ready() == false );

    // Check for Azimuth motor inversion
#ifdef REVERSE_AZIMUTH_MOTOR_DIRECTION
      while( i2cMotorDriver.busy() ); //Waits until the SCMD is available.
      i2cMotorDriver.inversionMode(0, 1); //invert Azimuth motor
#endif

    // Check for Altitude motor inversion
#ifdef REVERSE_ALTITUDE_MOTOR_DIRECTION
      while ( i2cMotorDriver.busy() ); //Waits until the SCMD is available.
      i2cMotorDriver.inversionMode(1, 1); //invert Altitude motor
#endif
  
    TCterminal.println("Waiting to enable outputs...");
    while ( i2cMotorDriver.busy() );
    i2cMotorDriver.enable(); //Enables the output driver hardware
    TCterminal.println("Motor driver board setup Done.");
  }
  
  // Since we expect the GPS to take a while to initialize, we do
  // telescope mount initialization here
  TCterminal.println("");
  TERMtextcolor('g');
  INIT();
  TERMtextcolor('c');
  TCterminal.println("");

  if ((ubloxGPS.begin() == false) || !I2CEEPROMpresent ) {
    //* We have to add in check for I2CEEPROMpresent, because if we don't
    // a bare board will end up getting a false positive for GPS present check.
    // This means that to use GPS, the system MUST have an I2C EEPROM present.
    // Ublox GPS NOT detected at default I2C address
    GPSpresent = false;
    // Assume Demo mode then
    GRYEAR = 2022;
    GRMONTH = 10;
    GRDAY = 1;
    rtcseconds = 0;
    rtchours = rtcmin = 1;
    SETIMEFLAG(); // Fake it!

    FALTEMP = (double)eecharbuf.strunion.ELEVATION; //Elevation in feet
    FLATITUDE = eecharbuf.strunion.FLATITUDE = 40.091125;
    FLONGITUDE = eecharbuf.strunion.FLONGITUDE = -105.18512;
    // */
    TERMtextcolor('r');
    TCterminal.println("U-blox based GPS NOT detected!");
    // TCterminal.println("Fix this first and Reboot!");
    // while (1) ;
  } else { // GPS online
    GPSpresent = true;
    TCterminal.println("U-blox based GPS detected.");
    TCterminal.println("Waiting to sync with GPS...");
    //ubloxGPS.setAutoPVT(true); // non-blocking mode
    ubloxGPS.setI2COutput(COM_TYPE_UBX); //Set the I2C port to output UBX only (turn off NMEA noise)
    ubloxGPS.saveConfigSelective(VAL_CFG_SUBSEC_IOPORT); //Save (only) the communications port settings to flash and BBR
    // We gotta wait until satellite sync is active
    while (((ubloxGPS.getLatitude() == 0) && (ubloxGPS.getLongitude() == 0)) || (ubloxGPS.getSIV() == 0)) {
      newdelay(1000); //wait one second between checks - any faster just makes noise
      TCterminal.print(".");
    }
    TCterminal.println("");
    GRYEAR = (int)ubloxGPS.getYear();
    GRMONTH = (byte)ubloxGPS.getMonth();
    GRDAY = (byte)ubloxGPS.getDay();
    rtchours = (byte)ubloxGPS.getHour();
    rtcmin = (byte)ubloxGPS.getMinute();
    rtcseconds = ubloxGPS.getSecond();
    FALTEMP = eecharbuf.strunion.ELEVATION = ubloxGPS.getAltitude() * 0.00328084; //Elevation in feet
    FLATITUDE = eecharbuf.strunion.FLATITUDE = ubloxGPS.getLatitude() / 10000000.;
    FLONGITUDE = eecharbuf.strunion.FLONGITUDE = ubloxGPS.getLongitude() / 10000000.;
    SETIMEFLAG(); // time is set correctly
  }
  //long Dtime = rtcseconds + (rtcmin * 60L) + (rtchours * 3600L);
  STRTturboCLK();
  myAstro.setLatLong(FLATITUDE, FLONGITUDE);
  myAstro.setTimeZone(eecharbuf.strunion.DTZONE);
  myAstro.setGMTdate(GRYEAR, GRMONTH, GRDAY);
  myAstro.setGMTtime(rtchours, rtcmin, rtcseconds);
  if (DSTAUTOFLAG) DSTFLAG = myAstro.useAutoDST();
  myAstro.getGMTsiderealTime();

  newdelay(500);
  irsetup = eecharbuf.strunion.IRSETUPflag; // Is IR table defined?
  irrecv.enableIRIn(); // Start the IR receiver

  SETIRFLAG(); // Fake it that IR is already set up
  SETTCIFLAG(); // Fake it that TC Options are already set up
  SETdisplayFLAG(); //Use default/EEPROM display options
  SETPIDFLAG(); //Use default/EEPROM motor PID values
  SETINITFLAG(); // Assume telescope mount is initialized
  if (MotorDriverflag && eecharbuf.strunion.enableRealHwInit) {
    if (getRockerTiltPresent()) rockerTilt.powerDownMode();
    if (getTubeTiltPresent()) tubeTilt.powerDownMode();
  }
  topEEPROMwrite();
}

void STRTturboCLK() {
  // Initialize registers, and set up RTC
  rtczero.begin(); // initialize RTC
  DateTime now = DateTime(GRYEAR, GRMONTH, GRDAY, rtchours, rtcmin, rtcseconds);
  rtczero.adjust(now);
}

void INITZONE() {
  float tmp = 0;
  // Time Zone?
  // Start by setting default
  // DTZONE already initialized in tcintro()
  TCterminal.println(" Type time zone offset from England.");
  TCterminal.println(" i.e. EST=-5, CST=-6, MST=-7, PST=-8, etc.");
  TCterminal.println(" Don't include Daylight Savings Time here.");
  do {
    TCterminal.print(" Time Zone=["); TCterminal.print(eecharbuf.strunion.DTZONE); TCterminal.print("]=");
    LCDclear(); LCDline1(); LCDprint("TZONE=["); LCDprint(eecharbuf.strunion.DTZONE, 2); LCDprint("]=");
    tmp = GETFDECNUM(eecharbuf.strunion.DTZONE);
    TCterminal.println("");
  } while (tmp < -12. || tmp > 12.);
  if (inputstrlen != 0) {
    eecharbuf.strunion.DTZONE = tmp;
    TCterminal.println("");
    TCterminal.println(" Is Daylight Savings Time currently in effect?");
    TCterminal.print(" DST IN? ["); TCterminal.print(DSTFLAG); TCterminal.print("]=");
    LCDclear(); LCDline1(); LCDprint("DST IN? ["); LCDprint(DSTFLAG); LCDprint("]=");
    DSTFLAG = GETYORN();
    eecharbuf.strunion.DSTFLAG = DSTFLAG;
    TCterminal.println("");
    DSTAUTOFLAG = false;
  }
}

void RESETIME() {
  TERMclear(); 
  INITZONE();
  SETIMEFLAG();
}

void StarTweak() {
  // Allow 'tweaking' values of azimuth offset and altitude offset
  int tmp = 1;
  eecharbuf.strunion.AZOFFSET = 0L; // Encoder count Offset of Azimuth Reference from True North
  eecharbuf.strunion.ALOFFSET = 0L; // Encoder count Offset of Altitude Horizon Reference from level
  int star1num, star2num, star3num, planetnum;
  int tweaknum[4] = { -1, -1, -1, -1 };
  double star1alt, star2alt, star3alt, planetalt;
  double tweakalt[4] = { 90.0, 90.0, 90.0, 90.0 };
  star1num = star2num = star3num = planetnum = -1;
  star1alt = star2alt = star3alt = planetalt = 90.0;
  double starRA, starDec;
  double tweakRA[4] = { 0., 0., 0., 0. };
  double tweakDec[4] = { 0., 0., 0., 0. };

  // 1. Scan bright star table to get 3 stars closest to 45 degrees altitude
  for (int i=0; i < NISTARS; i++) {
	  myObjects.selectStarTable(ISTARS[i]);
    starRA = myObjects.getRAdec();
    starDec = myObjects.getDeclinationDec();
	  myAstro.setRAdec(starRA, starDec);
	  if (eecharbuf.strunion.PFLAG) myAstro.doPrecessFrom2000();
	  starRA = myAstro.getRAdec();
    starDec = myAstro.getDeclinationDec();
	  myAstro.doRAdec2AltAz();
	  if (fabs(myAstro.getAltitude() - 45.) < tweakalt[0]) {
		  tweaknum[3] = tweaknum[2]; tweakRA[3] = tweakRA[2]; tweakDec[3] = tweakDec[2];
		  tweaknum[2] = tweaknum[1]; tweakRA[2] = tweakRA[1]; tweakDec[2] = tweakDec[1];
		  tweaknum[1] = tweaknum[0]; tweakRA[1] = tweakRA[0]; tweakDec[1] = tweakDec[0];
		  tweaknum[0] = i; tweakRA[0] = starRA; tweakDec[0] = starDec;
		  tweakalt[0] = fabs(myAstro.getAltitude() - 45.);
	  } else if (fabs(myAstro.getAltitude() - 45.) < tweakalt[1]) {
		  tweaknum[3] = tweaknum[2]; tweakRA[3] = tweakRA[2]; tweakDec[3] = tweakDec[2];
		  tweaknum[2] = tweaknum[1]; tweakRA[2] = tweakRA[1]; tweakDec[2] = tweakDec[1];
		  tweaknum[1] = i; tweakRA[1] = starRA; tweakDec[1] = starDec;
		  tweakalt[1] = fabs(myAstro.getAltitude() - 45.);
	  } else if (fabs(myAstro.getAltitude() - 45.) < tweakalt[2]) {
		  tweaknum[3] = tweaknum[2]; tweakRA[3] = tweakRA[2]; tweakDec[3] = tweakDec[2];
		  tweaknum[2] = i; tweakRA[2] = starRA; tweakDec[2] = starDec;
		  tweakalt[2] = fabs(myAstro.getAltitude() - 45.);
	  } else if (fabs(myAstro.getAltitude() - 45.) < tweakalt[3]) {
		  tweaknum[3] = i; tweakRA[3] = starRA; tweakDec[3] = starDec;
		  tweakalt[3] = fabs(myAstro.getAltitude() - 45.);
	  }
  }

  // Also check planets: Venus, Mars, Jupiter, Saturn
  for (int i=2; i < 7; i++) {
	  myObjects.selectStarTable(ISTARS[i]);
    if (i != 3) {
	    if (i == 2) myAstro.doVenus();
	    if (i == 4) myAstro.doMars();
	    if (i == 5) myAstro.doJupiter();
	    if (i == 6) myAstro.doSaturn();
	    starRA = myAstro.getRAdec();
      starDec = myAstro.getDeclinationDec();
	    myAstro.doRAdec2AltAz();
      if (fabs(myAstro.getAltitude() - 45.) < tweakalt[0]) {
	      tweaknum[3] = tweaknum[2]; tweakRA[3] = tweakRA[2]; tweakDec[3] = tweakDec[2];
		    tweaknum[2] = tweaknum[1]; tweakRA[2] = tweakRA[1]; tweakDec[2] = tweakDec[1];
		    tweaknum[1] = tweaknum[0]; tweakRA[1] = tweakRA[0]; tweakDec[1] = tweakDec[0];
		    tweaknum[0] = -i; tweakRA[0] = starRA; tweakDec[0] = starDec;
		    tweakalt[0] = fabs(myAstro.getAltitude() - 45.);
	    } else if (fabs(myAstro.getAltitude() - 45.) < tweakalt[1]) {
		    tweaknum[3] = tweaknum[2]; tweakRA[3] = tweakRA[2]; tweakDec[3] = tweakDec[2];
		    tweaknum[2] = tweaknum[1]; tweakRA[2] = tweakRA[1]; tweakDec[2] = tweakDec[1];
		    tweaknum[1] = -i; tweakRA[1] = starRA; tweakDec[1] = starDec;
		    tweakalt[1] = fabs(myAstro.getAltitude() - 45.);
	    } else if (fabs(myAstro.getAltitude() - 45.) < tweakalt[2]) {
		    tweaknum[3] = tweaknum[2]; tweakRA[3] = tweakRA[2]; tweakDec[3] = tweakDec[2];
		    tweaknum[2] = -i; tweakRA[2] = starRA; tweakDec[2] = starDec;
		    tweakalt[2] = fabs(myAstro.getAltitude() - 45.);
	    } else if (fabs(myAstro.getAltitude() - 45.) < tweakalt[3]) {
		    tweaknum[3] = -i; tweakRA[3] = starRA; tweakDec[3] = starDec;
		    tweakalt[3] = fabs(myAstro.getAltitude() - 45.);
	    }
    }
	}

  // 2. User selects one (First is default)
  TCterminal.println("\n Choose a star/planet to tweak the pointing algorithm.");
  if (eecharbuf.strunion.LCDserialflag || eecharbuf.strunion.LCDavrflag) {
    LCDclear();
    LCDline1();
    LCDprint("Pick Tweak Object");
    WAITASEC(5);
    LCDclear();
    LCDline1();
  }
  for (int i=0; i < 4; i++) {
    TCterminal.print(i+1);
    LCDprint(i+1);
    TCterminal.print(". ");
    LCDprint(". ");
    if (tweaknum[i] < 0) {
      PRPLANET(-tweaknum[i]); TCterminal.println("");
      PRPLANETlcd(-tweaknum[i]);
    } else {
      TCterminal.println(myObjects.printStarName(tweaknum[i]));
      LCDprint(myObjects.printStarName(tweaknum[i]));
    }
    if (i < 3) {
      LCDprint("\n");
    } else {
      LCDprint("  ");
    }
  }

  do {
    //TCterminal.print(" Object num=["); TCterminal.print(tmp); TCterminal.print("]=");
    //LCDclear(); LCDline1(); LCDprint("AzKp=["); LCDprint(eecharbuf.strunion.azKp, 2); LCDprint("]=");
    tmp = GETINUM();
    TCterminal.println("");
  } while (tmp > 4 || tmp < 1);
  tmp -= 1;

  // 3. Aim telescope to target star
  TRA = tweakRA[tmp];
  TDEC = tweakDec[tmp];
  myAstro.setRAdec( TRA, TDEC );
  myAstro.doRAdec2AltAz();
  // Refraction correction
  if (BMEpresent && eecharbuf.strunion.RFLAG) {
    myAstro.doRefractionF(FPINHG, FTEMPF);
  }
  TAZIMUTH = myAstro.getAzimuth();
  TALTITUDE = myAstro.getAltitude();
  gotoTarget();

  // 4. Request star centered manually
  TCterminal.println("\n Manually drive motors to center object in eyepiece:");
  TCterminal.println(" Press Lock button when done.");
  LCDclear();
  LCDline1();
  LCDprint("Center Object:");
  LCDline1();
  LCDprint("Hit Lock when Done");

  // 5. Handbox manipulation of pointing
  gotoTarget();

  // 6. Get Azimuth and Altitude encoder counts, and save the diffs as offsets for each axis
  //AzTweakOffsetCounts = ;
  //AlTweakOffsetCounts = ;
  // */
  return;
}

void INIT() {
  if (eecharbuf.strunion.enableRealHwInit) {
    if (getRockerTiltPresent()) rockerTilt.WakeMeUp();
    if (getTubeTiltPresent()) tubeTilt.WakeMeUp();
  // Initialize Telescope Mount
  // 1. Find Azimuth Reference
  // 2. Get Azimuth Range
  // 3. Check Azimuth Level
  if (!eecharbuf.strunion.AzRangeMeasured) {
    measureAZrange();
  } else {
    // Go to Azumuth Reference Sensor to zero encoder
    // Or, No Azimuth Reference Sensor available, and range is known, so just zero AZ encoder
    gotoAzRef();  // This zeros the enocder count for us
    driveMotorStop(AZIMUTH_MOTOR); // Stop Azimuth motor
    newdelay(500);
  }
  // 4. Get True North location in Azimuth, if possible
  // - Update Azimuth zero location
  getMagneticNorth();
  // 5. Get Horizon location in Altitude
  // 6. Get Range in Altitude by finding Zenith
  TCterminal.println("");
  TCterminal.println("Telescope Tube must be readied for observing now:");
  TCterminal.println("i.e. If it must be extended, do so.");
  TCterminal.println(hitkey);
  LCDclear();
  LCDline1();
  LCDprint("Extend Tube if");
  LCDline2();
  LCDprint("needed for use");
  LCDline4();
  LCDprint(hitkey);
  KEY();

  // 7. Check with reference star - done elsewhere
  StarTweak();
  
  if (MotorDriverflag && eecharbuf.strunion.enableRealHwInit) {
    if (getRockerTiltPresent()) rockerTilt.powerDownMode();
    if (getTubeTiltPresent()) tubeTilt.powerDownMode();
  }
  }
}

long initIRkey(long previous) {
  // Get IR input three identical times to proceed
  //char n, tabn;
  long x1, x2, x3, xn;
  x1 = x2 = 0L; x3 = 1L;
  do {
    if (irrecv.getResults()) {
      irdecoder.decode();  //Decode it
      // Return an IR input char if it has been repeated three times in a row
      xn = irdecoder.value;
      if (xn != 0xffffffffL) {
        TCterminal.println(xn, HEX);
        if (x2 != 0 && x3 == 1) {
          if (x1 == xn)
            x3 = x1;
          else
            x1 = x2 = 0;
        }

        if (x1 != 0 && x2 == 0) {
          if (x1 == xn)
            x2 = x1;
          else
            x1 = 0;
        }
        if (x1 == 0 ) x1 = xn;
        if (x1 == previous) x1 = 0L;
      }
      irrecv.enableIRIn(); // Receive the next value
    }
  } while (x1 != x2 || x2 != x3);

  return x1;
}

void RESETIR() {
  // IR remote use setup
  TCterminal.println(" ");
  TCterminal.println(" Need IR keys for: 0-9 - . <cr> <backspc> Right Left Up Down Lock");
  TCterminal.println(" And IR keys for: LCD Next Screen/Brighter/Dimmer Motors Faster/Slower");
  TCterminal.println(" Enable IR remote?");
  if (GETYORN()) { // Init IR decode array
    TCterminal.println("\n Press each key three times");
    TCterminal.print("\r 0"); eecharbuf.strunion.IRinput[0] = initIRkey(1L); eecharbuf.strunion.IRchar[0] = '0';
    TCterminal.print("\r 1"); eecharbuf.strunion.IRinput[1] = initIRkey(eecharbuf.strunion.IRinput[0]); eecharbuf.strunion.IRchar[1] = '1';
    TCterminal.print("\r 2"); eecharbuf.strunion.IRinput[2] = initIRkey(eecharbuf.strunion.IRinput[1]); eecharbuf.strunion.IRchar[2] = '2';
    TCterminal.print("\r 3"); eecharbuf.strunion.IRinput[3] = initIRkey(eecharbuf.strunion.IRinput[2]); eecharbuf.strunion.IRchar[3] = '3';
    TCterminal.print("\r 4"); eecharbuf.strunion.IRinput[4] = initIRkey(eecharbuf.strunion.IRinput[3]); eecharbuf.strunion.IRchar[4] = '4';
    TCterminal.print("\r 5"); eecharbuf.strunion.IRinput[5] = initIRkey(eecharbuf.strunion.IRinput[4]); eecharbuf.strunion.IRchar[5] = '5';
    TCterminal.print("\r 6"); eecharbuf.strunion.IRinput[6] = initIRkey(eecharbuf.strunion.IRinput[5]); eecharbuf.strunion.IRchar[6] = '6';
    TCterminal.print("\r 7"); eecharbuf.strunion.IRinput[7] = initIRkey(eecharbuf.strunion.IRinput[6]); eecharbuf.strunion.IRchar[7] = '7';
    TCterminal.print("\r 8"); eecharbuf.strunion.IRinput[8] = initIRkey(eecharbuf.strunion.IRinput[7]); eecharbuf.strunion.IRchar[8] = '8';
    TCterminal.print("\r 9"); eecharbuf.strunion.IRinput[9] = initIRkey(eecharbuf.strunion.IRinput[8]); eecharbuf.strunion.IRchar[9] = '9';
    TCterminal.print("\r -"); eecharbuf.strunion.IRinput[10] = initIRkey(eecharbuf.strunion.IRinput[9]); eecharbuf.strunion.IRchar[10] = '-';
    TCterminal.print("\r ."); eecharbuf.strunion.IRinput[11] = initIRkey(eecharbuf.strunion.IRinput[10]); eecharbuf.strunion.IRchar[11] = '.';
    TCterminal.print("\r <cr>"); eecharbuf.strunion.IRinput[12] = initIRkey(eecharbuf.strunion.IRinput[11]); eecharbuf.strunion.IRchar[12] = 0x0d;
    TCterminal.print("\r <backspc>"); eecharbuf.strunion.IRinput[13] = initIRkey(eecharbuf.strunion.IRinput[12]); eecharbuf.strunion.IRchar[13] = 0x08;
    TCterminal.print("\r Right    "); eecharbuf.strunion.IRinput[14] = initIRkey(eecharbuf.strunion.IRinput[13]); eecharbuf.strunion.IRchar[14] = 0x3e; // > greater than
    TCterminal.print("\r Left "); eecharbuf.strunion.IRinput[15] = initIRkey(eecharbuf.strunion.IRinput[14]); eecharbuf.strunion.IRchar[15] = 0x3c; // < less than
    TCterminal.print("\r Up  "); eecharbuf.strunion.IRinput[16] = initIRkey(eecharbuf.strunion.IRinput[15]); eecharbuf.strunion.IRchar[16] = 0x5e; // ^ Caret
    TCterminal.print("\r Down"); eecharbuf.strunion.IRinput[17] = initIRkey(eecharbuf.strunion.IRinput[16]); eecharbuf.strunion.IRchar[17] = 0x76; // v lowercase letter V
    TCterminal.print("\r Lock"); eecharbuf.strunion.IRinput[18] = initIRkey(eecharbuf.strunion.IRinput[17]); eecharbuf.strunion.IRchar[18] = 0x0d; // CR
    TCterminal.print("\r LCD next Screen"); eecharbuf.strunion.IRinput[19] = initIRkey(eecharbuf.strunion.IRinput[18]); eecharbuf.strunion.IRchar[19] = 'n';
    TCterminal.print("\r LCD Brighter"); eecharbuf.strunion.IRinput[20] = initIRkey(eecharbuf.strunion.IRinput[19]); eecharbuf.strunion.IRchar[20] = '+';
    TCterminal.print("\r LCD Dimmer"); eecharbuf.strunion.IRinput[21] = initIRkey(eecharbuf.strunion.IRinput[20]); eecharbuf.strunion.IRchar[21] = '=';
    TCterminal.print("\r Motors Faster"); eecharbuf.strunion.IRinput[22] = initIRkey(eecharbuf.strunion.IRinput[21]); eecharbuf.strunion.IRchar[22] = 'f';
    TCterminal.print("\r Motors Slowe"); eecharbuf.strunion.IRinput[23] = initIRkey(eecharbuf.strunion.IRinput[22]); eecharbuf.strunion.IRchar[23] = 's';
    eecharbuf.strunion.IRSETUPflag = irsetup = true;
  } else {
    eecharbuf.strunion.IRSETUPflag = irsetup = false;
  }
  SETIRFLAG();
}

void OptionStateMsg(boolean flag) {
  //Print out Option state
  if (flag) {
    TERMtextcolor('g');
    TCterminal.println("Enabled");
  } else {
    TERMtextcolor('r');
    TCterminal.println("Disabled");
  }
  TERMtextcolor('w');
}

void LCDOptionStateMsg(boolean flag) {
  //Print out Option state
  if (flag) {
    LCDprint("E");
  } else {
    LCDprint("D");
  }
}

void RESETTCI() {
  // Set up basic telescope interface parameters
  // i.e. Ranges, etc.
  char choice = 'A';

  do {
    TCterminal.println("\n Select Option to Enable/Disable");
    TCterminal.print(" 1) INA219 Voltage Monitor: ");    OptionStateMsg(eecharbuf.strunion.INA219flag);
    TCterminal.print(" 2) Motor Driver: ");    OptionStateMsg(eecharbuf.strunion.MotorDriverflag);
    TCterminal.print(" 3) Limit Switches: ");    OptionStateMsg(eecharbuf.strunion.USELIMITS);
    TCterminal.print(" 4) Precession: ");    OptionStateMsg(eecharbuf.strunion.PFLAG);
    TCterminal.print(" 5) Refraction: ");    OptionStateMsg(eecharbuf.strunion.RFLAG);
    TCterminal.print(" 6) Site ID: ");
    TERMtextcolor('g');   TCterminal.println(eecharbuf.strunion.SiteID);    TERMtextcolor('w');
	  TCterminal.print(" 7) Real Telescope Hardware: "); OptionStateMsg(eecharbuf.strunion.enableRealHwInit);
    TCterminal.println(" 0) Done - Return to Main Display");
    LCDclear();
    //LCDline1(); LCDprint("1 Blank:");
    LCDprint(" 2 MTR:"); LCDOptionStateMsg(eecharbuf.strunion.MotorDriverflag);
    LCDline2(); LCDprint("3 Lim:"); LCDOptionStateMsg(eecharbuf.strunion.USELIMITS);
    LCDprint(" 4 Prec:"); LCDOptionStateMsg(eecharbuf.strunion.PFLAG);
    LCDline3(); LCDprint("5 Ref:"); LCDOptionStateMsg(eecharbuf.strunion.RFLAG);
    LCDprint(" 0 Done"); 
    LCDline4(); LCDprint("6:");
    LCDprint(eecharbuf.strunion.SiteID);
    LCDprint(" 7 RealHw:"); LCDOptionStateMsg(eecharbuf.strunion.enableRealHwInit);
    choice = KEY();
    if (choice == '2') {
      eecharbuf.strunion.MotorDriverflag = !(eecharbuf.strunion.MotorDriverflag);
	    MotorDriverflag = eecharbuf.strunion.MotorDriverflag;
	}
    if (choice == '3') eecharbuf.strunion.USELIMITS = !(eecharbuf.strunion.USELIMITS);
    if (choice == '4') eecharbuf.strunion.PFLAG = !(eecharbuf.strunion.PFLAG);
    if (choice == '5') eecharbuf.strunion.RFLAG = !(eecharbuf.strunion.RFLAG);
    if (choice == '6') {
      // Redefine Site ID
      TCterminal.print("\n Enter new Site ID: ");
      LCDclear();
      LCDline1(); LCDprint("Enter new Site ID:"); 
      LCDline2();
      inputstrlen = ACCEPT(eecharbuf.strunion.SiteID, 39); //Get 39 chars max
      TCterminal.println(" ");
    }
	if (choice == '7') {
    LCDclear();
    LCDline1(); LCDprint("Are you sure? (y/n)");
    TCterminal.print("Are you sure? (y/n)");
    if (GETYORN()) eecharbuf.strunion.enableRealHwInit = !(eecharbuf.strunion.enableRealHwInit);
	}
  } while (choice != '0');
  if (MotorDriverflag && eecharbuf.strunion.enableRealHwInit) {
    if (getRockerTiltPresent()) rockerTilt.powerDownMode();
    if (getTubeTiltPresent()) tubeTilt.powerDownMode();
  } else {
    if (getRockerTiltPresent()) rockerTilt.WakeMeUp();
    if (getTubeTiltPresent()) tubeTilt.WakeMeUp();
  }
  SETTCIFLAG();
}

void RESETdisplay() {
  // Set up Display options
  char choice = 'A';

  do {
    TCterminal.println("\n Select Option to Enable/Disable");
    TCterminal.print(" 2) Serial LCD Display: ");    OptionStateMsg(eecharbuf.strunion.LCDserialflag);
    TCterminal.print(" 3) AVR LCD Display: ");    OptionStateMsg(eecharbuf.strunion.LCDavrflag);
    TCterminal.print(" 4) Serial Terminal Display: ");    OptionStateMsg(eecharbuf.strunion.SerialTermflag);
    TCterminal.println(" 0) Done - Return to Main Display");
    LCDclear();
    LCDline1(); LCDprint("0 Done");
    LCDline2(); LCDprint("2 Serial LCD:"); LCDOptionStateMsg(eecharbuf.strunion.LCDserialflag);
    if (eecharbuf.strunion.LCDserialflag) {
      LCDprint(" +-");
    }
    LCDline3(); LCDprint("3 AVR LCD:"); LCDOptionStateMsg(eecharbuf.strunion.LCDavrflag);
    
    LCDline4(); LCDprint("4 Serial:"); LCDOptionStateMsg(eecharbuf.strunion.SerialTermflag);
    choice = KEY();
    if (choice == '2') eecharbuf.strunion.LCDserialflag = !(eecharbuf.strunion.LCDserialflag);
    if (choice == '3') eecharbuf.strunion.LCDavrflag = !(eecharbuf.strunion.LCDavrflag);
    if ((choice == '-') && eecharbuf.strunion.LCDserialflag) {
      LCDbrightness--;
      if (LCDbrightness < 0x80) LCDbrightness = 0x80;
      TC_LCD.write(0x7C); //Send command character
      TC_LCD.write(LCDbrightness);
      newdelay(500);
    } else if ((choice == '+') && eecharbuf.strunion.LCDserialflag) {
      LCDbrightness++;
      if (LCDbrightness > 0x9D) LCDbrightness = 0x9D;
      TC_LCD.write(0x7C); //Send command character
      TC_LCD.write(LCDbrightness);
      newdelay(500);
    }
    if (choice == '4') {
      eecharbuf.strunion.SerialTermflag = !(eecharbuf.strunion.SerialTermflag);
    }
  } while ((choice != '0') || !(eecharbuf.strunion.SerialTermflag || eecharbuf.strunion.LCDserialflag || eecharbuf.strunion.LCDavrflag));
  SETdisplayFLAG();
}

void RESETPID() {
  TCterminal.println(" Update Motor PID parameters.");
  TCterminal.println(" For each paramter, press ENTER to accept the current value.\n");
  float tmp = 0;
  do {
    TCterminal.print(" Azimuth Kp=["); TCterminal.print(eecharbuf.strunion.azKp); TCterminal.print("]=");
    LCDclear(); LCDline1(); LCDprint("AzKp=["); LCDprint(eecharbuf.strunion.azKp, 2); LCDprint("]=");
    tmp = GETFDECNUM(eecharbuf.strunion.azKp);
    TCterminal.println("");
  } while (tmp < -120. || tmp > 120.);
  if (inputstrlen != 0) {
    azKp = eecharbuf.strunion.azKp = tmp;
    TCterminal.println("");
  }
  do {
    TCterminal.print(" Azimuth Ki=["); TCterminal.print(eecharbuf.strunion.azKi); TCterminal.print("]=");
    LCDline2(); LCDprint("AzKi=["); LCDprint(eecharbuf.strunion.azKi, 2); LCDprint("]=");
    tmp = GETFDECNUM(eecharbuf.strunion.azKi);
    TCterminal.println("");
  } while (tmp < -120. || tmp > 120.);
  if (inputstrlen != 0) {
    azKi = eecharbuf.strunion.azKi = tmp;
    TCterminal.println("");
  }
  do {
    TCterminal.print(" Azimuth Kd=["); TCterminal.print(eecharbuf.strunion.azKd); TCterminal.print("]=");
    LCDline3(); LCDprint("AzKd=["); LCDprint(eecharbuf.strunion.azKd, 2); LCDprint("]=");
    tmp = GETFDECNUM(eecharbuf.strunion.azKd);
    TCterminal.println("");
  } while (tmp < -120. || tmp > 120.);
  if (inputstrlen != 0) {
    azKd = eecharbuf.strunion.azKd = tmp;
    TCterminal.println("");
  }
  TCterminal.print(" Azimuth N must be in the range 3 <= N <= 10");
  do {
    TCterminal.print(" Azimuth N=["); TCterminal.print(eecharbuf.strunion.azN); TCterminal.print("]=");
    LCDline4(); LCDprint("AzN=["); LCDprint(eecharbuf.strunion.azN, 2); LCDprint("]=");
    tmp = GETFDECNUM(eecharbuf.strunion.azN);
    TCterminal.println("");
  } while (tmp < 3. || tmp > 10.);
  if (inputstrlen != 0) {
    azN = eecharbuf.strunion.azN = tmp;
    TCterminal.println("");
  }
  do {
    TCterminal.print(" Altitude Kp=["); TCterminal.print(eecharbuf.strunion.alKp); TCterminal.print("]=");
    LCDclear(); LCDline1(); LCDprint("AlKp=["); LCDprint(eecharbuf.strunion.alKp, 2); LCDprint("]=");
    tmp = GETFDECNUM(eecharbuf.strunion.alKp);
    TCterminal.println("");
  } while (tmp < -120. || tmp > 120.);
  if (inputstrlen != 0) {
    alKp = eecharbuf.strunion.alKp = tmp;
    TCterminal.println("");
  }
  do {
    TCterminal.print(" Altitude Ki=["); TCterminal.print(eecharbuf.strunion.alKi); TCterminal.print("]=");
    LCDline2(); LCDprint("AlKi=["); LCDprint(eecharbuf.strunion.alKi, 2); LCDprint("]=");
    tmp = GETFDECNUM(eecharbuf.strunion.alKi);
    TCterminal.println("");
  } while (tmp < -120. || tmp > 120.);
  if (inputstrlen != 0) {
    alKi = eecharbuf.strunion.alKi = tmp;
    TCterminal.println("");
  }
  do {
    TCterminal.print(" Altitude Kd=["); TCterminal.print(eecharbuf.strunion.alKd); TCterminal.print("]=");
    LCDline3(); LCDprint("AlKd=["); LCDprint(eecharbuf.strunion.alKd, 2); LCDprint("]=");
    tmp = GETFDECNUM(eecharbuf.strunion.alKd);
    TCterminal.println("");
  } while (tmp < -120. || tmp > 120.);
  if (inputstrlen != 0) {
    alKd = eecharbuf.strunion.alKd = tmp;
    TCterminal.println("");
  }
  TCterminal.print(" Altitude N must be in the range 3 <= N <= 10");
  do {
    TCterminal.print(" Altitude N=["); TCterminal.print(eecharbuf.strunion.alN); TCterminal.print("]=");
    LCDline4(); LCDprint("AlN=["); LCDprint(eecharbuf.strunion.alN, 2); LCDprint("]=");
    tmp = GETFDECNUM(eecharbuf.strunion.alN);
    TCterminal.println("");
  } while (tmp < 3. || tmp > 10.);
  if (inputstrlen != 0) {
    alN = eecharbuf.strunion.alN = tmp;
    TCterminal.println("");
  }
}

void topEEPROMwrite() {
  if ( tcEEPROM.write(2L + EEOFFSET, eecharbuf.ebuf, sizeof(EEstruct)) != 0 ) {
    //there was a problem
    TCterminal.println("EEPROM write error.");
    TCterminal.println(hitkey);
    LCDline4(); LCDprint("EEPROM write error ");
    KEY();
  }
  byte tmpbyte = EEcheckByte;
  tcEEPROM.write(0L + EEOFFSET, &tmpbyte, 1);
  printstatusscreen();
}

void gotoTarget() {
  // Start process of moving motors to Target Right Ascension (TRA) and Declination (TDEC)
  // Compute Target Azimuth/Altitude Encoder count values
  long targetAzCnt = (TAZIMUTH / 360.) * RRAAZ;
  long targetAlCnt = (TALTITUDE / 90.) * RDECAL;
  //*
  if (magOffsetComputed) {
  TcRAAZ = targetAzCnt - AzimuthMagneticEncoderOffset - magVariationInAzimuthCounts + eecharbuf.strunion.AZOFFSET;
  } else {
  TcRAAZ = targetAzCnt + eecharbuf.strunion.AZOFFSET;
  }
  // */
  RAAZ = RAAZenc.read();
  if (TcRAAZ - RAAZ > 0L) {
    startMotorToTarget(AZIMUTH_MOTOR, CW_DIRECTION, RAAZ, TcRAAZ);
  } else if (TcRAAZ - RAAZ < 0L) {
    startMotorToTarget(AZIMUTH_MOTOR, CCW_DIRECTION, RAAZ, TcRAAZ);
  }
  // Compute Target encoder counts in Declination/Altitude
  TcDECAL = targetAlCnt + eecharbuf.strunion.ALOFFSET;
  //DECAL = DECALenc.read();
  if (TcDECAL - DECAL > 0L) {
    // Start Altitude Motor CW towards Zenith
    startMotorToTarget(ALTITUDE_MOTOR, CW_DIRECTION, DECAL, TcDECAL);
  } else if (TcDECAL - DECAL < 0L) {
    startMotorToTarget(ALTITUDE_MOTOR, CCW_DIRECTION, DECAL, TcDECAL);
  }
}

void doCommand() {
  // Process command key press from user
  int tmp = 0;
  long int Ltmp = 0L;
  screenCOMMAND = STAYFUNC;
  char num = KEY();
  if (num == 0x08) {
    // Initialization menu
    TERMclear();
    TCterminal.println(" Initialization menu");
    TCterminal.println(" 1 Time");
    TCterminal.println(" 2 Orientation");
    TCterminal.println(" 3 IR decode");
    TCterminal.println(" 4 TC Options");
    TCterminal.println(" 5 Display");
	  TCterminal.println(" 6 Motor PID Parameters");
    LCDclear();
    LCDline1(); LCDprint("1 Time  2 Mount");
    LCDline2(); LCDprint("3 IR  4 Options");
    LCDline3(); LCDprint("5 Display  6 PID");
    num = KEY();
    // Reinit on Backspace
    if (num == '1') RESETIMEFLAG();
    if (num == '2') RESETINITFLAG();
    if (num == '3') RESETIRFLAG();
    if (num == '4') RESETTCIFLAG();
    if (num == '5') RESETdisplayFLAG();
	if (num == '6') RESETPIDFLAG();
    if ((num < '1') || (num > '6')) {
      printstatusscreen();
      //LCDclear();
    }
  } else if (num < '9' && num >= '0') {
    // Sun, Moon, or Planet
    COMMAND = num - '0';
    switch (COMMAND) {
      case 0: myAstro.doSun(); break;
      case 1: myAstro.doMercury(); break;
      case 2: myAstro.doVenus(); break;
      case 3: myAstro.doMoon(); myAstro.doLunarParallax(); break;
      case 4: myAstro.doMars(); break;
      case 5: myAstro.doJupiter(); break;
      case 6: myAstro.doSaturn(); break;
      case 7: myAstro.doUranus(); break;
      case 8: myAstro.doNeptune(); break;
    }
    TRA = myAstro.getRAdec();
    TDEC = myAstro.getDeclinationDec();
  } else if ( num == '9') {
    // Arbitrary
    Ltmp = -1L;
    TERMclear();

    TCterminal.println(" Input in hour.minute.second format:");
    do {
      LCDclear();  LCDline1(); LCDprint("RA=");
      TCterminal.print(" Right Ascension = ");
      Ltmp = INPUTHMS(); TCterminal.println("");
    } while (Ltmp < 0 || Ltmp > (24L * 3600L));
    if (Ltmp != -1L) {
      TRA = (double)Ltmp / 3600.; // Convert RA to hours
    }
    TCterminal.println(" ");
    TCterminal.println(" Input in degree.minute.second format:");
    Ltmp = -90L * 3600L;
    do {
      TCterminal.print(" Declination = ");
      LCDline1(); LCDprint("Dec=");
      Ltmp = INPUTHMS(); TCterminal.println("");
    } while (Ltmp < (-90L * 3600L) || Ltmp > (90L * 3600L));
    if (Ltmp != (-90L * 3600L)) {
      TDEC = (double)Ltmp / 3600.; // Convert Declination to hours
      COMMAND = '9' - '0';
    }
    double Dtmp = 0.;
    if (eecharbuf.strunion.PFLAG) {
        do {
          LCDclear();  LCDline3(); LCDprint("Epoch=");
          TCterminal.print(" Epoch (year) = ");
          Dtmp = GETFDECNUM(); TCterminal.println("");
        } while (Dtmp < 1600. || Ltmp > (2200.));
      myAstro.setGMTdate((long)Dtmp,1,1);
        myAstro.setRAdec(TRA, TDEC);
      myAstro.doPrecessTo2000();
        myAstro.setGMTdate(GRYEAR, GRMONTH, GRDAY);
        myAstro.doPrecessFrom2000();
        TRA = myAstro.getRAdec();
        TDEC = myAstro.getDeclinationDec();
    }
    printstatusscreen();
  } else if ( num == '.') {
    // Star
    TERMclear();
    LCDclear();  LCDline1();
    int j = 0;
    int k = (int)myObjects.printStarName(1);
    for (int i = 0; i <= myObjects.NSTARS; i++) {
      if ((int)myObjects.printStarName(i) != k) {
        TCterminal.print(i);
        TCterminal.print(" ");
        TCterminal.print(myObjects.printStarName(i));
        TCterminal.print("   ");
        j++;
      }
      if (j > 4) {
        j = 0;
        TCterminal.println("");
      }
    }
    TCterminal.println("");
    TCterminal.print(" Input Star number between 1 and ");
    TCterminal.println(myObjects.NSTARS);
    do {
      LCDclear();  LCDline1();  LCDprint("Star=");
      TCterminal.print(" Star Number = ");
      tmp = GETINUM(0);
      TCterminal.println("");
    } while (tmp <= 0 || tmp > myObjects.NSTARS);
    if (tmp != 0) {
      myObjects.selectStarTable(tmp);
      TRA = myObjects.getRAdec();
      TDEC = myObjects.getDeclinationDec();
      COMMAND = FNDARB;
	  if (eecharbuf.strunion.PFLAG) {
        myAstro.setRAdec(TRA, TDEC);
        myAstro.doPrecessFrom2000();
        TRA = myAstro.getRAdec();
        TDEC = myAstro.getDeclinationDec();
	  }
    }
    printstatusscreen();
  } else if (num == '-') {
    // Non-stellar object menu
    TERMclear();
    TCterminal.println(" Non-stellar Object menu");
    TCterminal.println(" 1 NGC");
    TCterminal.println(" 2 IC");
    TCterminal.println(" 3 Other Object table");
    TCterminal.println(" 4 Messier");
    TCterminal.println(" 5 Caldwell");
    TCterminal.println(" 6 Hershel 400");
    TCterminal.println(" 7 Return to Display Screen");
    LCDclear();  LCDline1(); LCDprint("1 NGC 2 IC  3 Other");
    LCDline2(); LCDprint("4 Messr  5 Caldwell");
    LCDline3(); LCDprint("6 Herschel 400");
    char num1 = KEY();

    if (num1 == '1') {
      do {
        LCDclear();  LCDline1(); LCDprint("NGC=");
        TCterminal.print(" NGC Number = ");
        tmp = GETDDECNUM();
        TCterminal.println("");
      } while (tmp < 0 || tmp > myObjects.NGCNUM);
      if (tmp != 0) {
        myObjects.selectNGCTable(tmp);
        doPrecessObject();
      }
    }
    if (num1 == '2') {
      do {
        TCterminal.print(" IC Number = ");
        LCDclear();  LCDline1(); LCDprint("IC=");
        tmp = GETDDECNUM();
        TCterminal.println("");
      } while (tmp < 0 || tmp > myObjects.ICNUM);
      if (tmp != 0) {
        myObjects.selectICTable(tmp);
        doPrecessObject();
      }
    }
    if (num1 == '3') {
      do {
        TCterminal.print(" Other Object Table Number = ");
        LCDclear();  LCDline1(); LCDprint("Other=");
        tmp = GETDDECNUM();
        TCterminal.println("");
      } while (tmp < 0 || tmp > 32000);
      if (tmp != 0) {
        if (myObjects.selectOtherObjectsTable(tmp)) {
          doPrecessObject();
        }
      }
    }
    if (num1 == '4') {
      do {
        TCterminal.print(" Messier Number = ");
        LCDclear();  LCDline1(); LCDprint("Messier=");
        tmp = GETDDECNUM();
        TCterminal.println("");
      } while (tmp < 0 || tmp > 110);
      if (tmp != 0) {
        myObjects.selectMessierTable(tmp);
        doPrecessObject();
      }
    }
    if (num1 == '5') {
      do {
        TCterminal.print(" Caldwell Number = ");
        LCDclear();  LCDline1(); LCDprint("Caldwell=");
        tmp = GETDDECNUM();
        TCterminal.println("");
      } while (tmp < 0 || tmp > 109);
      if (tmp != 0) {
        myObjects.selectCaldwellTable(tmp);
        doPrecessObject();
      }
    }
    if (num1 == '6') {
      do {
        TCterminal.print(" Herschel 400 Number = ");
        LCDclear();  LCDline1(); LCDprint("Hershel=");
        tmp = GETDDECNUM();
        TCterminal.println("");
      } while (tmp < 0 || tmp > 400);
      if (tmp != 0) {
        myObjects.selectHershel400Table(tmp);
        doPrecessObject();
      }
    }
    printstatusscreen();
  } else if (num == 'n') {
    LCDclear();
    LCDscreenNum++;
    if (LCDscreenNum > 4) LCDscreenNum = 0;
  } else if (num == 0x0d) {
    // Goto previously specified Target position
    if (MotorDriverflag && eecharbuf.strunion.enableRealHwInit) {
      gotoTarget();
    }
  } else if (num == '+') {
    LCDbrighter();
  } else if (num == '=') {
    LCDdimmer();
  }
}

void doPrecessObject() {
  TRA = myObjects.getRAdec();
  TDEC = myObjects.getDeclinationDec();
  COMMAND = FNDOBJECT;
  if (eecharbuf.strunion.PFLAG) {
    myAstro.setRAdec(TRA, TDEC);
    myAstro.doPrecessFrom2000();
    TRA = myAstro.getRAdec();
    TDEC = myAstro.getDeclinationDec();
  }
}

// Main Telescope Controller Routines
void tcintro() { // Startup screen for user
  // Set up I2C and serial ports
  
  Serial.begin(9600); //May use VT100 compatible terminal emulator - Full Menus
  //while (!Serial); //Wait for user to open terminal
  newdelay(2000);
  Serial.println(" Start with Test of Serial Output.");
  Wire.begin(); // I2C init
  
  Serial1.begin(9600); // use serial 4x20 LCD display - Easy to mount onto telescope
  
  // For SAMD51 Serial2
  pinPeripheral(4, PIO_SERCOM); // Define Pins for Serial2 UART port
  pinPeripheral(7, PIO_SERCOM);
  Serial2.begin(9600); //Or put VT100 compatible terminal emulator - Full Menus here
  
  newdelay(1600); // Give time for Serial2 to init
  TERMclear(); //Clear terminal screen and home cursor
  TERMtextcolor('g');
  TCterminal.println("\nArduino SAMD51 Telescope Controller");
  TCterminal.print("Version ");
  TCterminal.println(tcversion);
  TCterminal.println("(c) 2022-2026, MIT License");
  TERMtextcolor('r');
  TCterminal.println("\nThis software provided as-is without warranty of any kind.");
  TCterminal.println("The User assumes all responsibility for use of this");
  TCterminal.println("program and all related documentation files.");
  TERMtextcolor('w');
  TCterminal.print("\nInitializing system for ");
  TCterminal.print("Alt-Azimuth");
  TCterminal.println(" mounted telescopes.");
  
  TCterminal.println("");

  // This was the first half of the topmost Forth word TC - used for initialization
  TERMtextcolor('c');
  inithardware(); //See what we have out there connected, and set it up

  /* Site ID string copy to sized buffer (overflow safe): */
  strncpy ( siteid, eecharbuf.strunion.SiteID, sizeof(eecharbuf.strunion.SiteID) );

  //Handle Lock btn status on Reset
  if (lockbtninitflag) { //Lock button pressed on reset?
    TCterminal.println("\nLock button pressed on reset.  Forcing reinitialization.");
    LCDline2();
    LCDprint("TC SYSTEM RESET");
    RESETIMEFLAG(); RESETINITFLAG(); // Actual re-initialization done in TC_main()
    eepromDefaults();
    WAITASEC(3); // Let user know what we've done
  }
  // make it so it doesn't assume errors on start
  if (NOTIMESETquestion() && !INITFLAG) {
    RESETERRFLAG();
  }

  WAITASEC(2);
  //LCDline3();
  //LCDprint(hitkey);
  LCDscreenNum = 3;
  TERMtextcolor('w');
  //TCterminal.println(hitkey);
  //KEY();
  TCterminal.println("    ");
  printstatusscreen();
  COMMAND = STAYFUNC; // Dummy command value to start
  screenCOMMAND = COMMAND;
}

void TC_main() {
  // Do telescope initialization here to allow for re-initialization by user selection
  if (NOTIMESETquestion()) {
    RESETIME();
    topEEPROMwrite();
  }
  if (NOTINITquestion()) {
    if (MotorDriverflag) {
      INIT(); // Initialize telescope
      topEEPROMwrite();
    }
    SETINITFLAG();
  }
  if (IRquestion()) {
    RESETIR(); // Initialize IR remote key decoding
    topEEPROMwrite();
  }
  if (TCIquestion()) {
    RESETTCI(); // Initialize telescope options
    topEEPROMwrite();
  }
  if (Displayquestion()) {
    RESETdisplay(); // Initialize display options
    topEEPROMwrite();
  }
  if (PIDquestion()) {
    RESETPID(); // Update Motor PID parameters
    topEEPROMwrite();
  }
  // Main processing loop
  updatestatusscreen(); // Update Serial Status screen, if enabled, and compute current state
  if (eecharbuf.strunion.LCDserialflag || eecharbuf.strunion.LCDavrflag) updatestatusLCD();
  if (CHKNUM()) {
    doCommand();
  }
}
