DavidArmstrong/SAMDTelescopeController/TC4_0/tcdervio.ino

/* Telescope Controller 4.00.00 - Derived I/O functions
// September 2022
// See MIT LICENSE.md file and ReadMe.md file for essential information
// Highly tailored to the AdaFruit M4 Metro
// DO NOT ATTEMPT TO LOAD THIS ONTO A STANDARD UNO */

#include "tcheader.h"

void printDegMinSecs(double n) {
  boolean sign = (n < 0.);
  if (sign) n = -n;
  long lsec = n * 360000.0;
  long deg = lsec / 360000;
  long min = (lsec - (deg * 360000)) / 6000;
  float secs = (lsec - (deg * 360000) - (min * 6000)) / 100.;
  if (sign) TCterminal.print("-");
  if (abs(deg) < 10) {
    TCterminal.print("0");
  }
  TCterminal.print(deg); TCterminal.print(":");
  if (abs(min) < 10) {
    TCterminal.print("0");
  }
  TCterminal.print(min); TCterminal.print(":");
  if (abs(secs) < 10) {
    TCterminal.print("0");
  }
  TCterminal.print((int)abs(secs)); TCterminal.print(" ");
}

void printDegMinSecsLCD(double n) {
  boolean sign = (n < 0.);
  if (sign) n = -n;
  long lsec = n * 360000.0;
  long deg = lsec / 360000;
  long min = (lsec - (deg * 360000)) / 6000;
  float secs = (lsec - (deg * 360000) - (min * 6000)) / 100.;
  if (sign) LCDprint("-");
  if (abs(deg) < 10) {
    LCDprint("0");
  }
  LCDprint(deg); LCDprint(":");
  if (abs(min) < 10) {
    LCDprint("0");
  }
  LCDprint(min); LCDprint(":");
  if (abs(secs) < 10) {
    LCDprint("0");
  }
  LCDprint((int)abs(secs)); LCDprint(" ");
}

void printTime(double n) {
  boolean sign = (n < 0.);
  if (sign) n = -n;
  long lsec = n * 3600.0;
  long deg = lsec / 3600;
  long min = (lsec - (deg * 3600)) / 60;
  float secs = (lsec - (deg * 3600) - (min * 60));
  //if (sign) TCterminal.print("-");
  print2digitsUSB(deg); TCterminal.print(":");
  print2digitsUSB(min); TCterminal.print(":");
  print2digitsUSB(abs(secs)); TCterminal.print(" ");
}

void printTimeLCD(double n) {
  boolean sign = (n < 0.);
  if (sign) n = -n;
  long lsec = n * 3600.0;
  long deg = lsec / 3600;
  long min = (lsec - (deg * 3600)) / 60;
  float secs = (lsec - (deg * 3600) - (min * 60));
  //if (sign) TCterminal.print("-");
  print2digitsLCD(deg); LCDprint(":");
  print2digitsLCD(min); LCDprint(":");
  print2digitsLCD(abs(secs)); LCDprint(" ");
}

void print2digitsUSB(int number) {
  if (number < 10) {
    TCterminal.print("0");
  }
  TCterminal.print(number);
}

void print2digitsLCD(int number) {
  if (eecharbuf.strunion.LCDavrflag) {
    Wire.beginTransmission(LCDi2c_ADR);
    if (number < 10) {
      Wire.print("0");
    }
    Wire.print(number);
    Wire.endTransmission();
  } else if (eecharbuf.strunion.LCDserialflag) {
    if (number < 10) {
      TC_LCD.print("0");
    }
    TC_LCD.print(number);
  }
}

boolean TRPLCMP( int n1, int n2, int n3, int n4 ) {
  return (n4 == n1) || (n4 == n2) || (n4 == n3);
}

boolean GETYORN() { // True for Yes, False for No
  char n;
  boolean flag;
  do {
    n = KEY();
    flag = ((n == '0') || (n == '1')
            || (n == 'N') || (n == 'n')
            || (n == 'Y') || (n == 'y'));
  } while ( !flag );
  EMIT(n); // echo good input
  return TRPLCMP('Y', '1', 'y', n);
}

long GETDDECNUM() {
  // read a line from user into buffer, return char count
  char PAD[10];
  inputstrlen = ACCEPT( PAD, 10 );
  return GETnum(PAD); //converted string to long
}

int GETINUM() {
  return (int)GETDDECNUM();
}

int GETINUM(int n) {
  // read a line from user into buffer, return char count
  char PAD[10];
  inputstrlen = ACCEPT( PAD, 10 );
  if (inputstrlen == 1) return n;
  return (int)GETnum(PAD); //converted string to long
}

long CONVHMS(char *buf) { // return d seconds
  // Convert an input string in hour.minutes.seconds format to a long
  long secs = 0L; // return seconds
  int x;
  int y = 0;
  int countdots = 0;
  hmsseconds = hmsmin = hmshours = 0;
  //Assume string is no longer than 20 characters
  for (x = 0; x < 20; x++) {
    if (buf[x] == '.') {
      //A decimal point means we need to move to the next units
      hmshours = hmsmin;
      hmsmin = hmsseconds;
      secs += (long)y;
      hmsseconds = y;
      if (countdots > 1) return secs;
      secs *= 60L;
      countdots++;
      y = 0;
    } else if (buf[x] == 0) {
      //Done converting
      if (countdots == 0) {
        hmshours = y;
        secs = y * 3600L;
      } else if (countdots == 1) {
        hmshours = hmsmin;
        hmsmin = y;
        secs = (y + secs) * 60L;
        hmsseconds = 0;
      } else {
        hmshours = hmsmin;
        hmsmin = hmsseconds;
        secs += (long)y;
        hmsseconds = y;
      }
      return secs;
    } else {
      // add in the next digit
      y = (y * 10) + (buf[x] - '0');
    }
  }
  // The routine will never get here, but the compiler complains anyway
  return secs;
}

long INPUTHMS() {
  char PAD[13];
  inputstrlen = ACCEPT(PAD, 12); //Get 12 chars max
  if (PAD[0] == '-') {
    //Minus sign present
    PAD[0] = '0'; //remove the sign char to get a positive number
    return -1L * CONVHMS(PAD);
  } else {
    return CONVHMS(PAD);
  }
}

double GETFDECNUM() {
  //Get a floating point number from user, in int.fraction format
  //Allow for negative numbers
  char PAD[13];
  int inputstrlen;
  inputstrlen = ACCEPT(PAD, 12); //Get 12 chars max
  return atof(PAD);
}

double GETFDECNUM(float n) {
  //Get a floating point number from user, in int.fraction format
  //Allow for negative numbers
  char PAD[13];
  int inputstrlen;
  inputstrlen = ACCEPT(PAD, 12); //Get 12 chars max
  if (inputstrlen == 1) return n;
  return atof(PAD);
}
